xian-cong/Swalk-Stick/JPEG/2 - Content Page.jpg

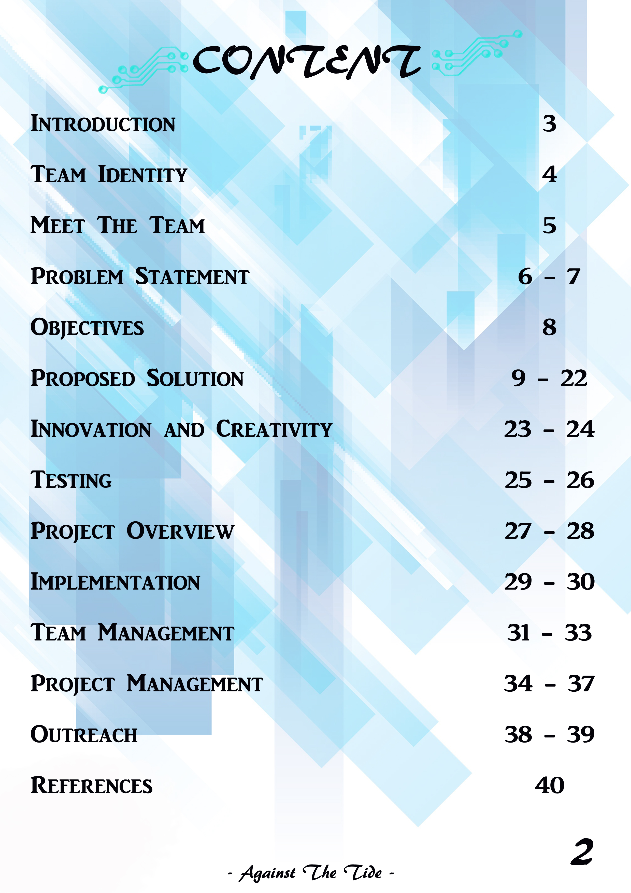
JPEG/2 - Content Page.jpg
