xian-cong/Swalk-Stick/JPEG/4 - Team Identity.jpg

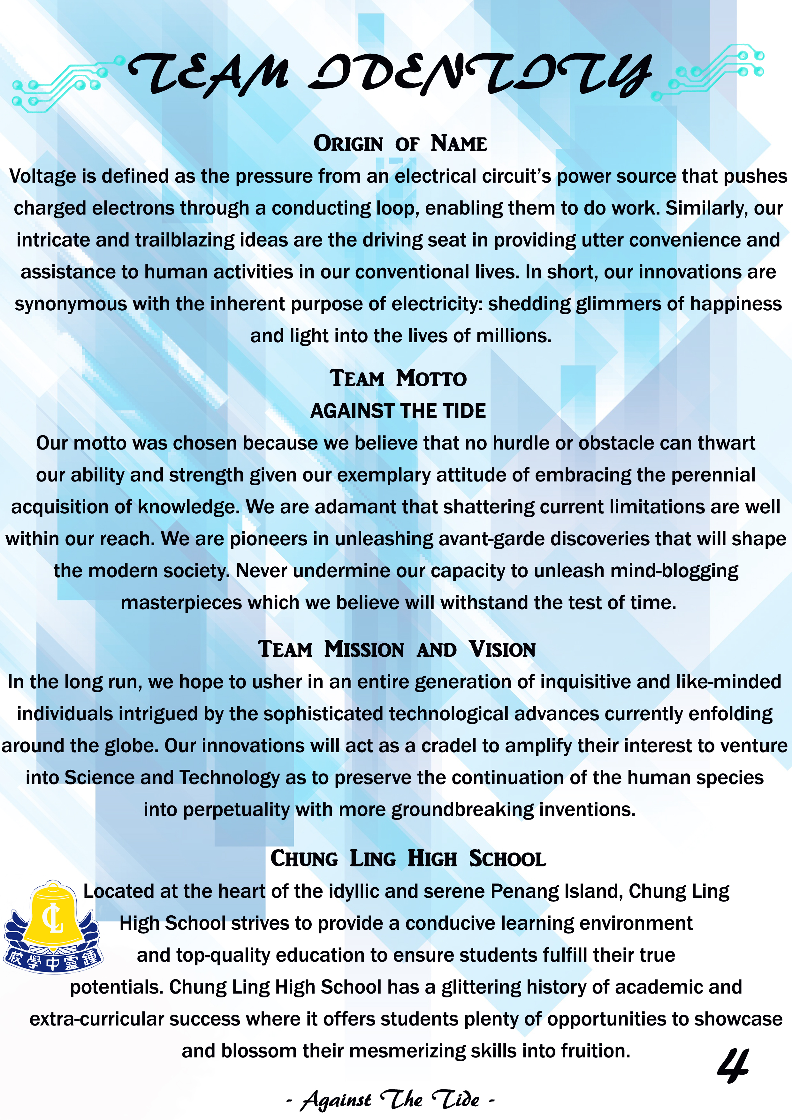
JPEG/4 - Team Identity.jpg
