xian-cong/Swalk-Stick/JPEG/5 - Meet The Team.jpg

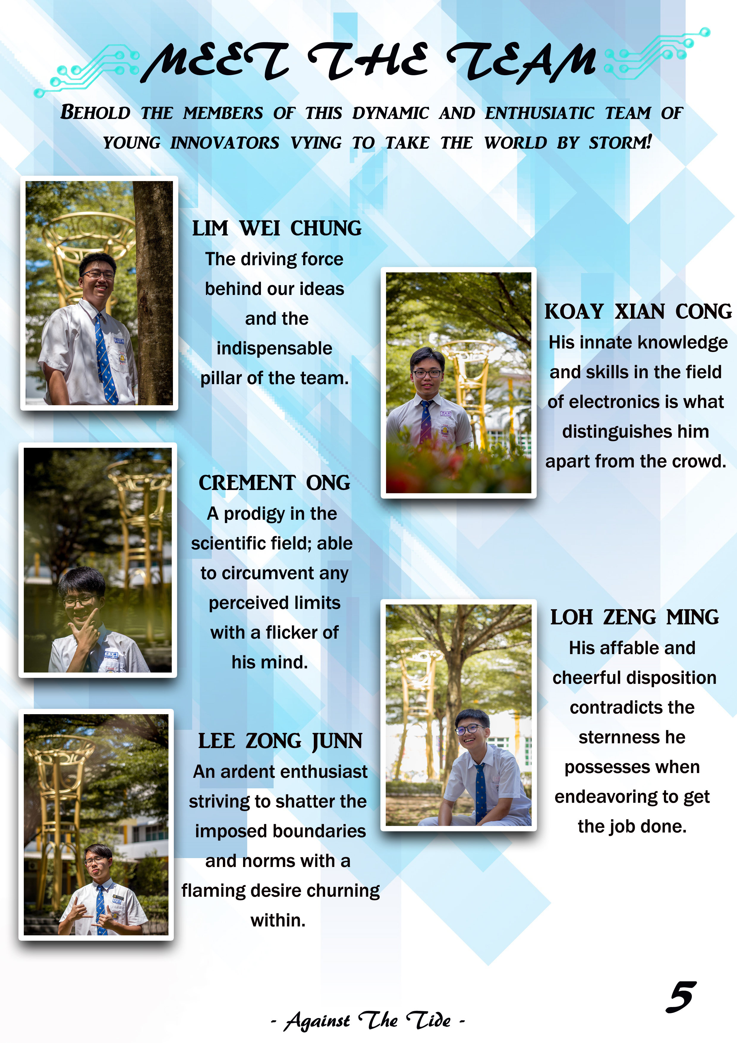
JPEG/5 - Meet The Team.jpg
