xian-cong/Swalk-Stick/JPEG/7 - Problem Statement.jpg

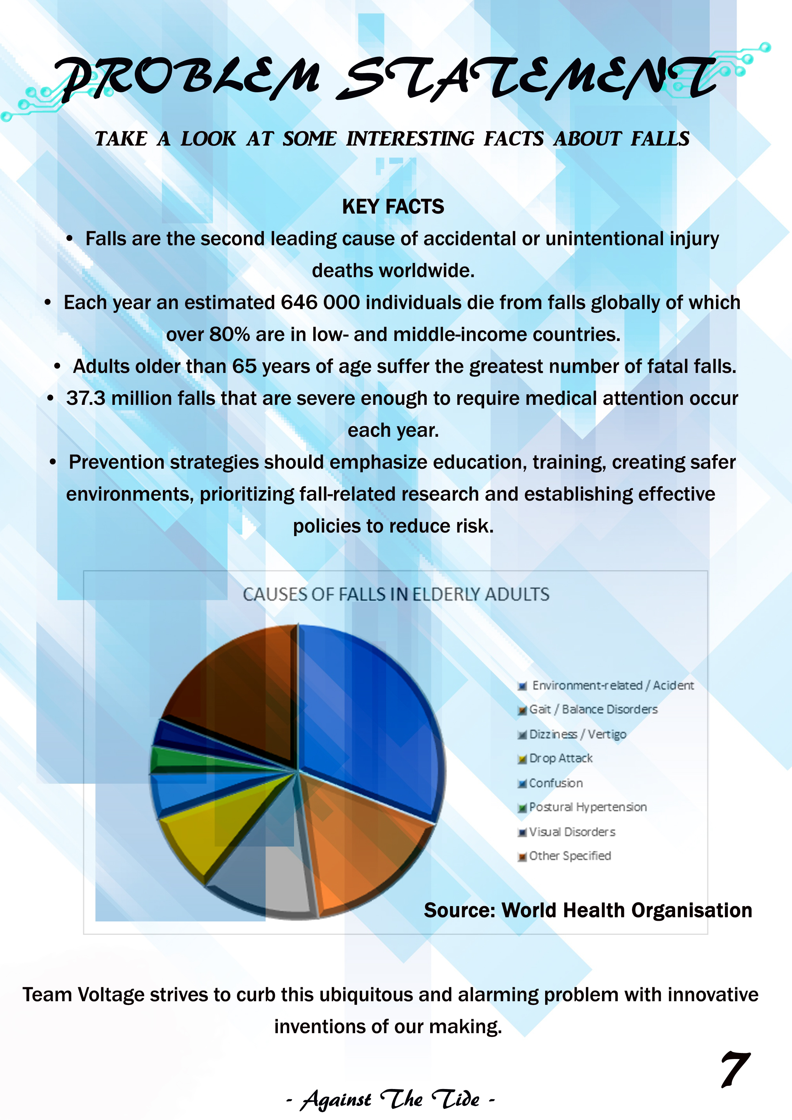
JPEG/7 - Problem Statement.jpg
