xian-cong/Swalk-Stick/JPEG/8 - Objectives.jpg

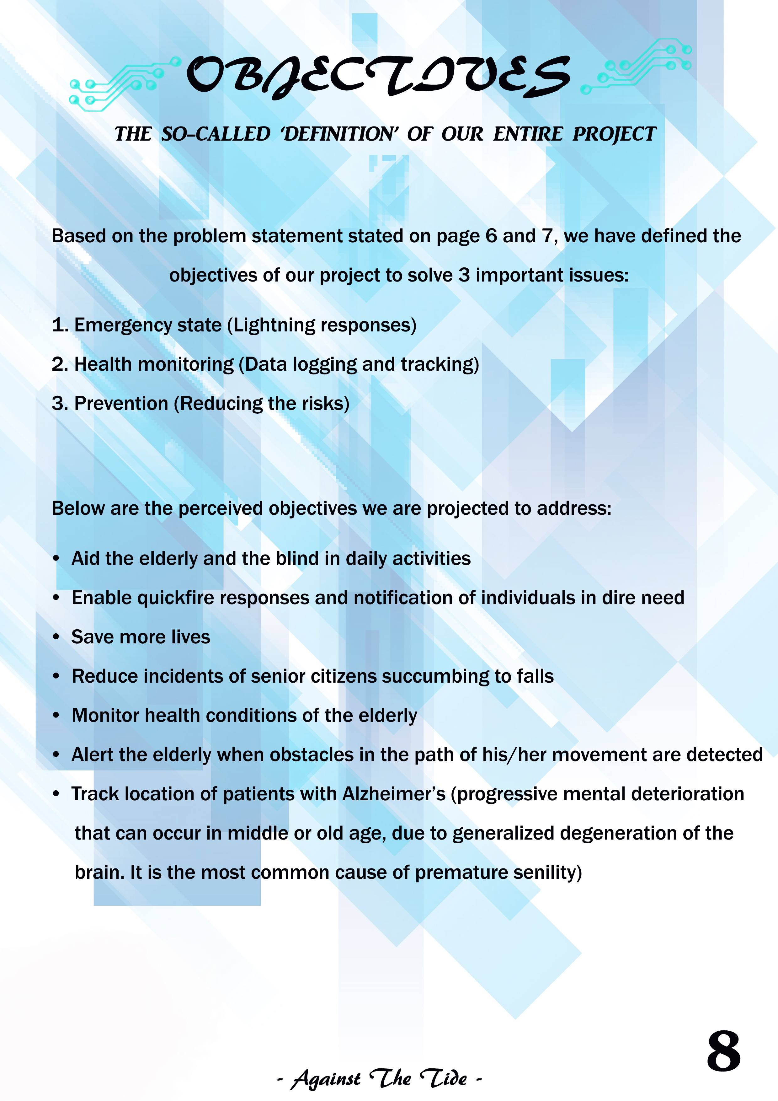
JPEG/8 - Objectives.jpg
