xian-cong/Swalk-Stick/JPEG/11 - Solution (Function).jpg

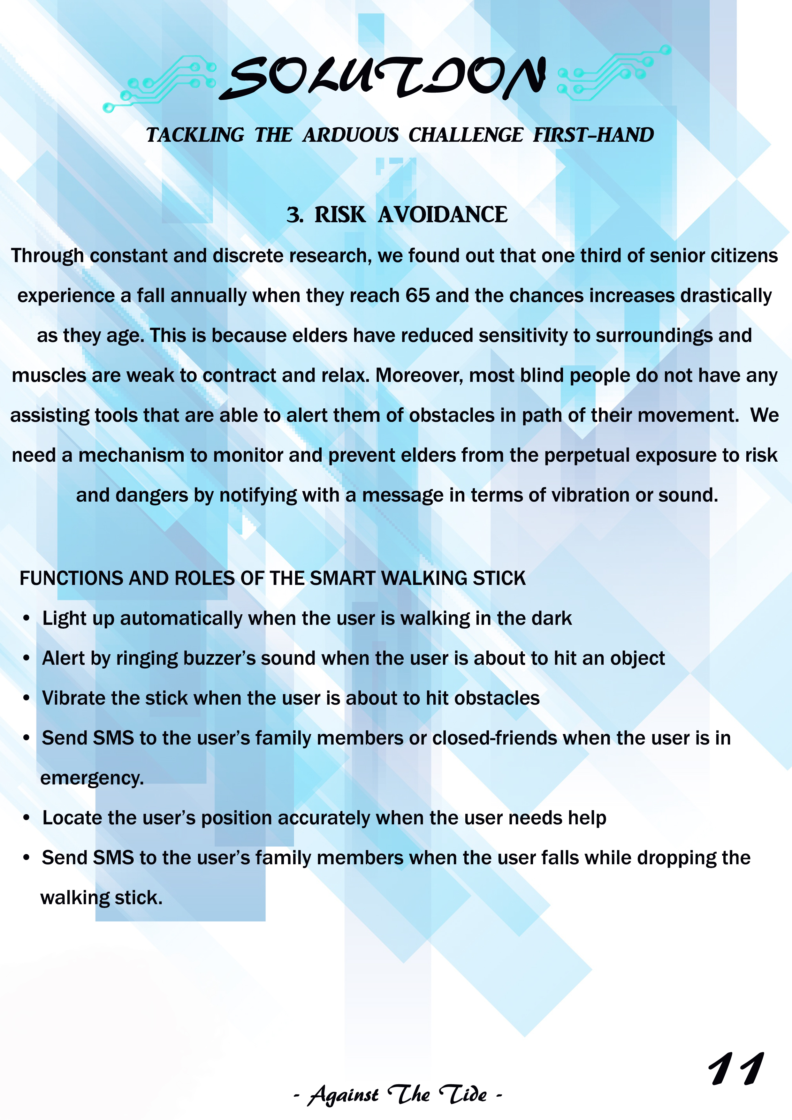
JPEG/11 - Solution (Function).jpg
