xian-cong/Swalk-Stick/JPEG/12 - Solution (Design Specifications).jpg

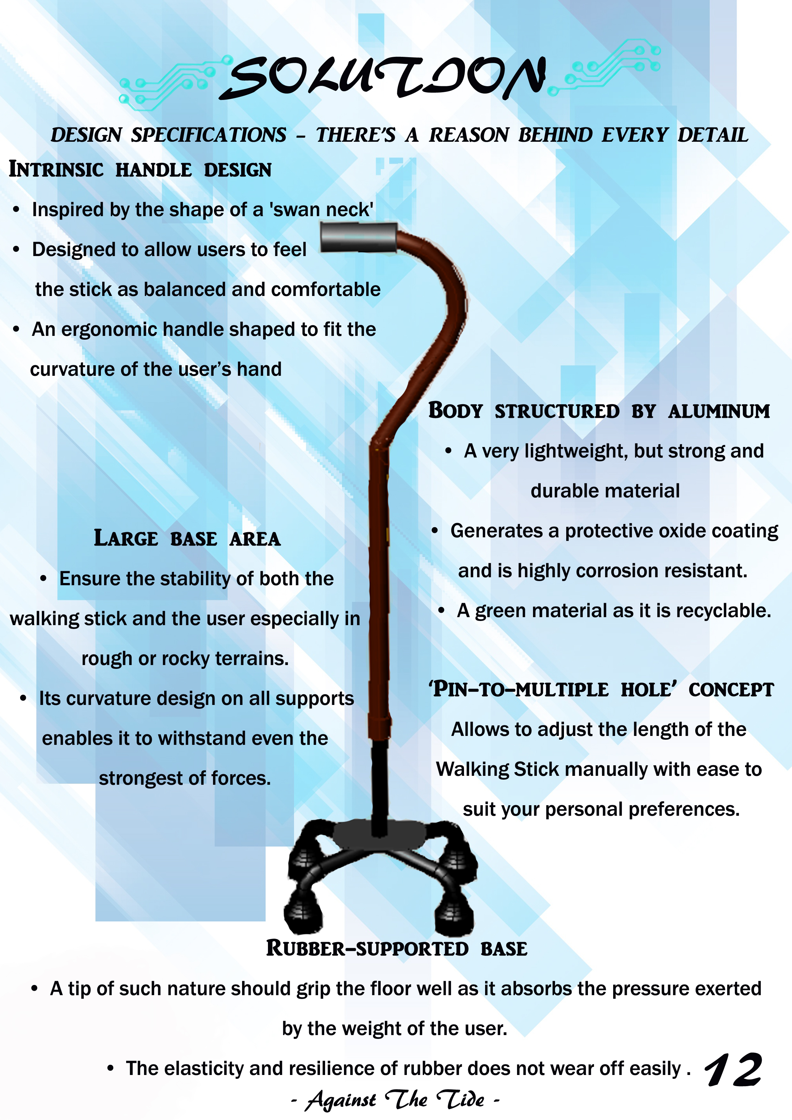
JPEG/12 - Solution (Design Specifications).jpg
