xian-cong/Swalk-Stick/JPEG/14 - Solution (Hardware I).jpg

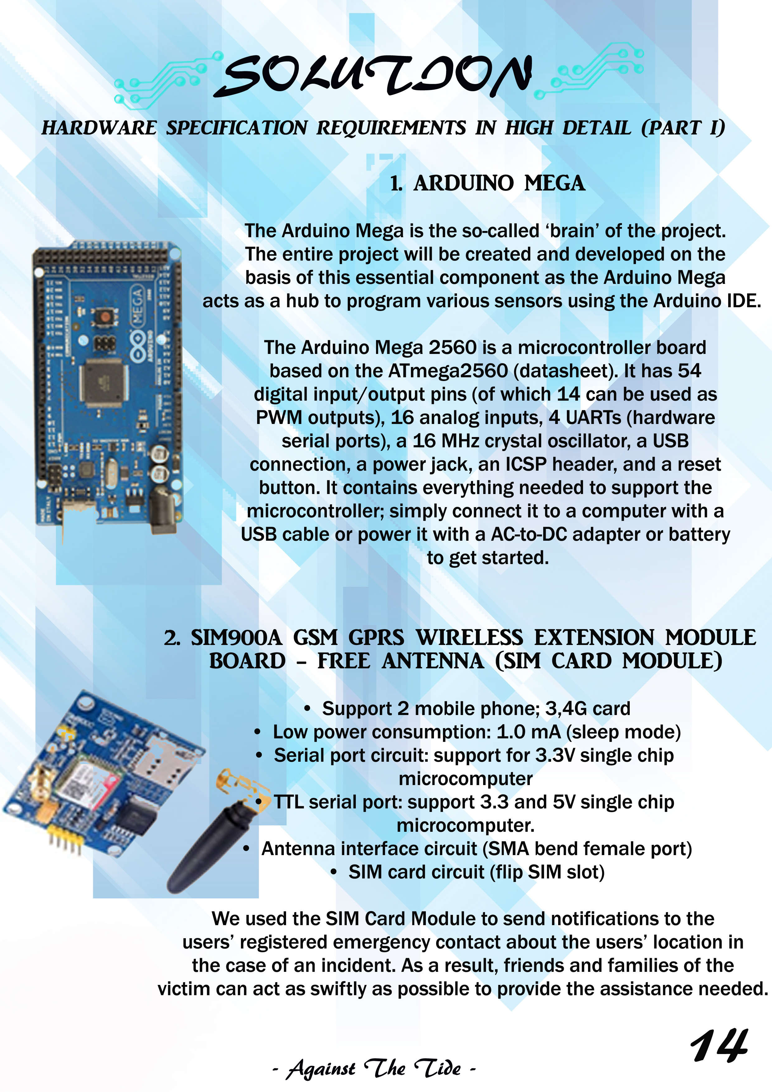
JPEG/14 - Solution (Hardware I).jpg
