xian-cong/Swalk-Stick/JPEG/16 - Solution (Hardware III).jpg

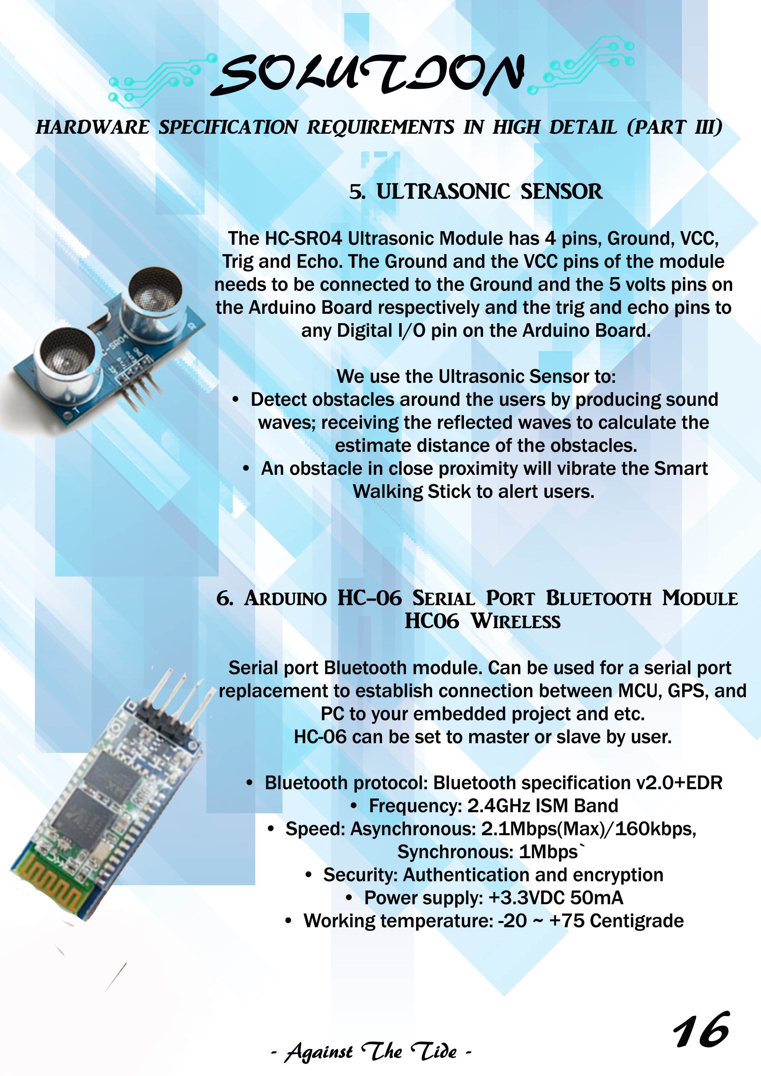
JPEG/16 - Solution (Hardware III).jpg
