xian-cong/Swalk-Stick/JPEG/17 - Solution (Hardware IV).jpg

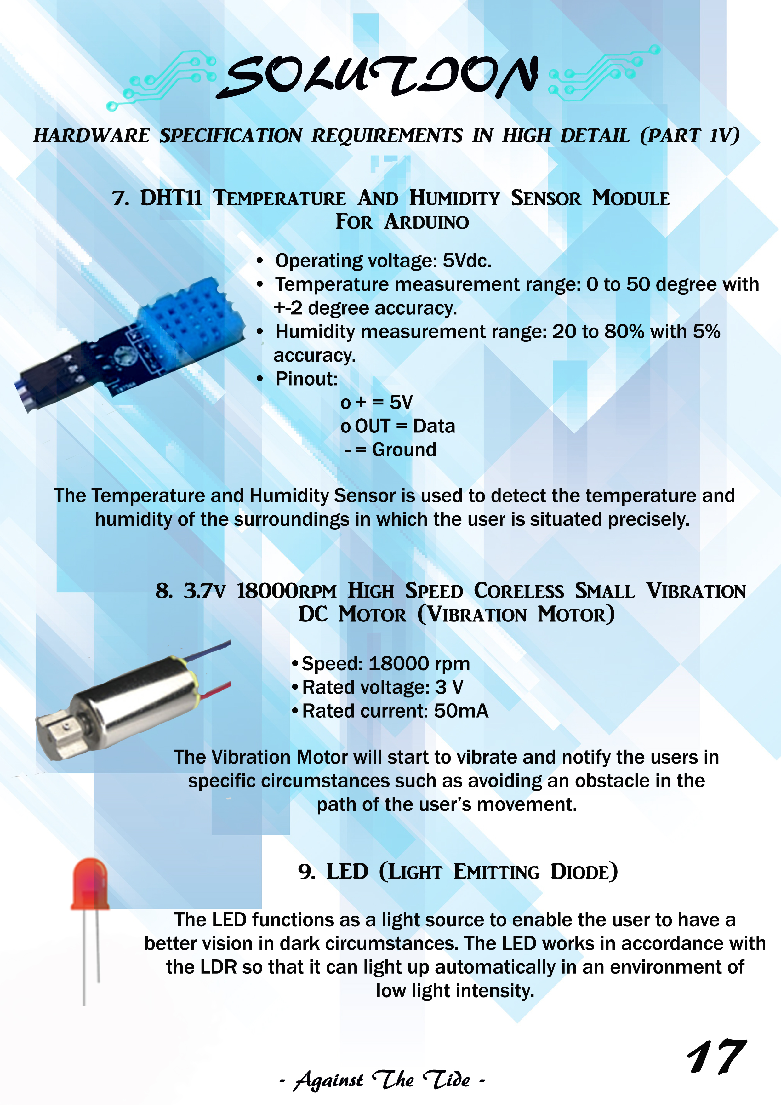
JPEG/17 - Solution (Hardware IV).jpg
