xian-cong/Swalk-Stick/JPEG/22 -Solution (Summary).jpg

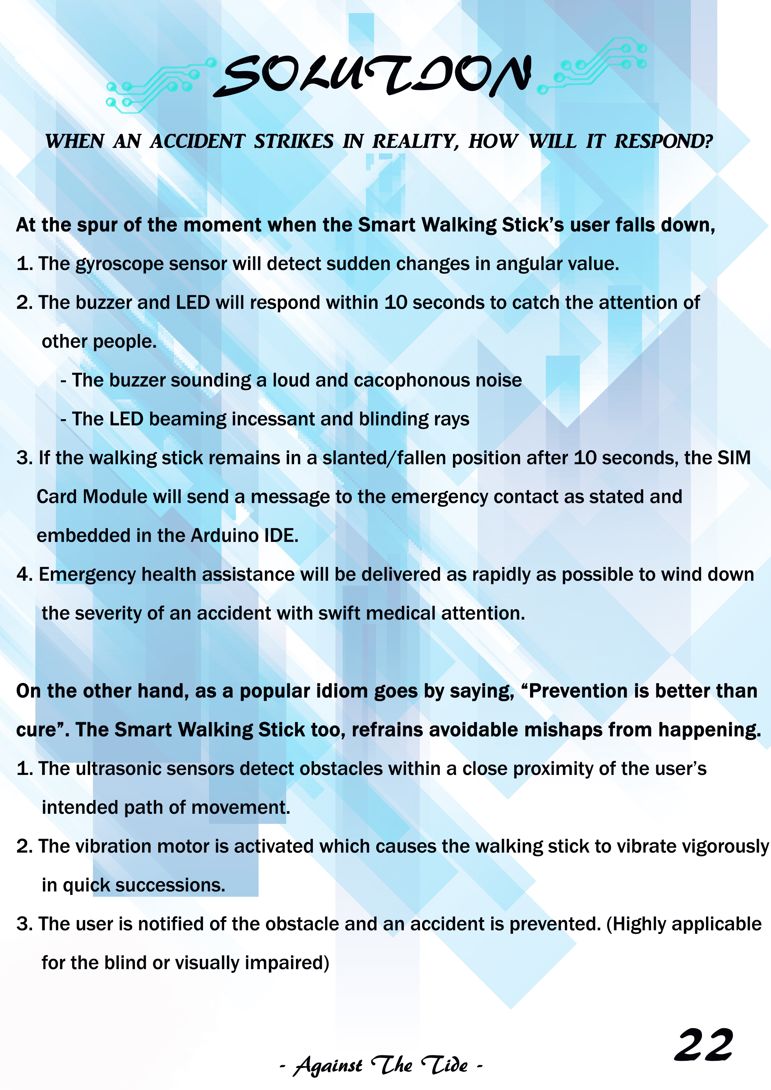
JPEG/22 -Solution (Summary).jpg
