xian-cong/Swalk-Stick/JPEG/23 - Creativity and Innovation.jpg

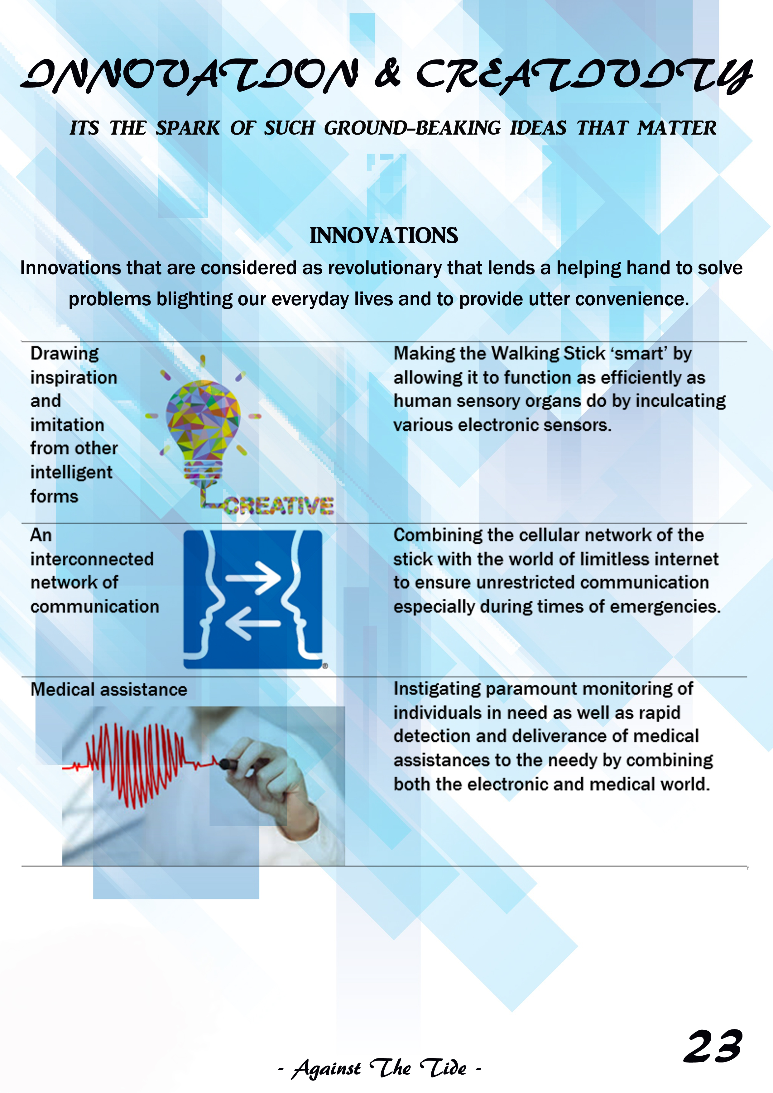
JPEG/23 - Creativity and Innovation.jpg
