xian-cong/Swalk-Stick/JPEG/24 - Innovation and Creativity II.jpg

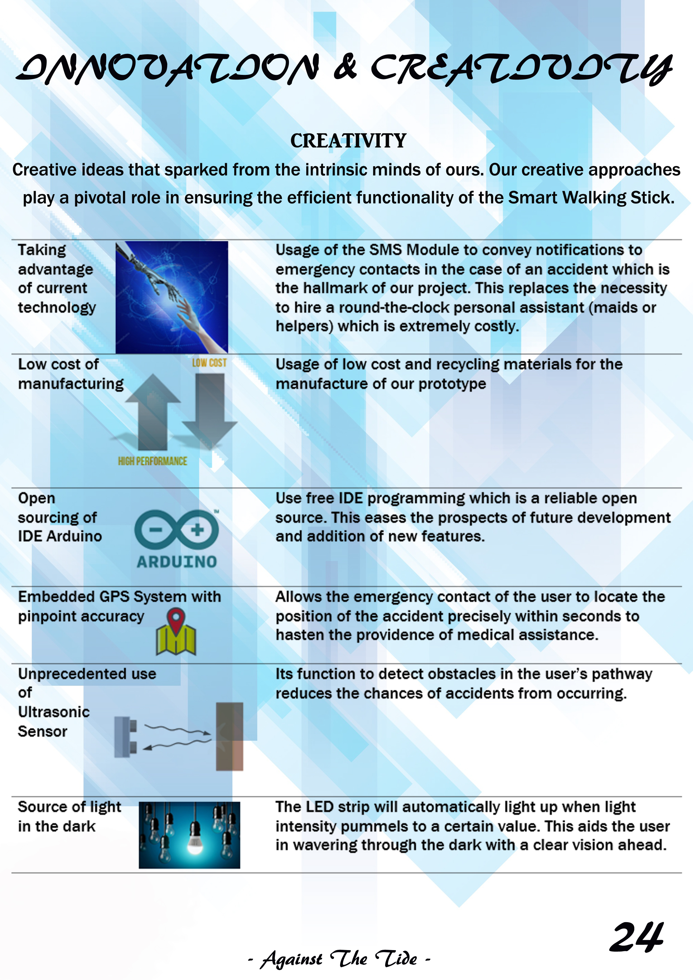
JPEG/24 - Innovation and Creativity II.jpg
