xian-cong/Swalk-Stick/JPEG/27 - Project Overview I.jpg

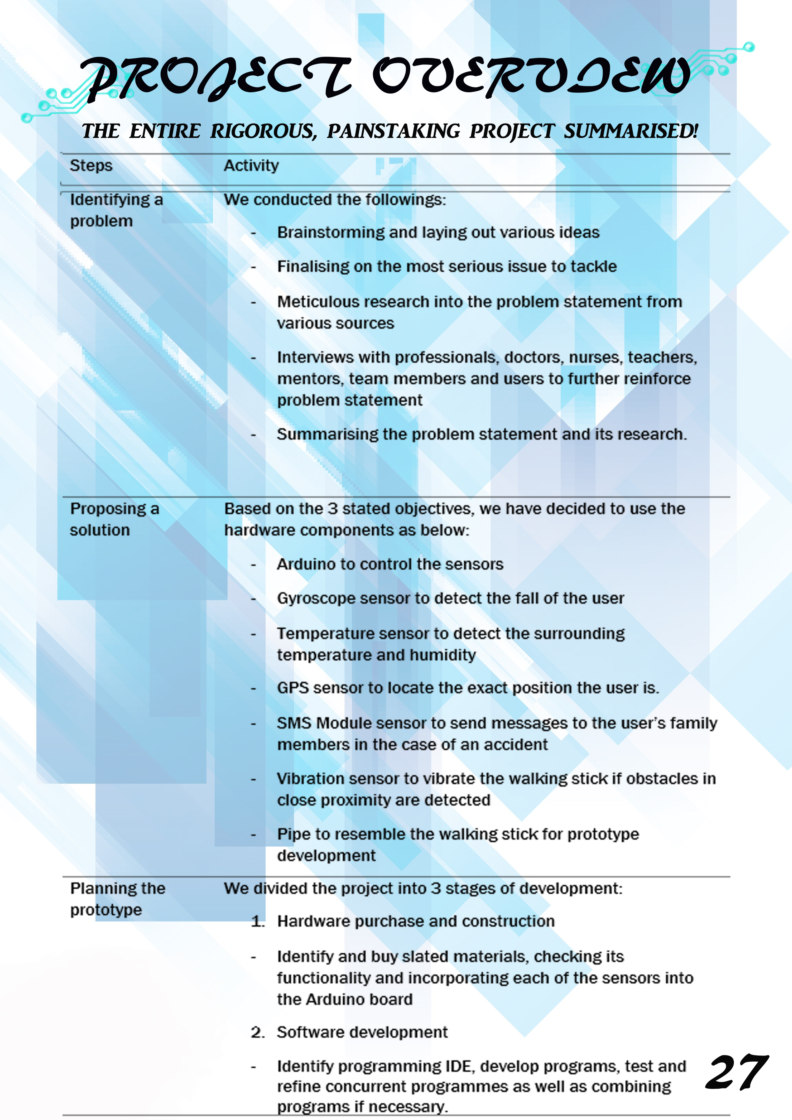
JPEG/27 - Project Overview I.jpg
