xian-cong/Swalk-Stick/JPEG/29 - Implementation I.jpg

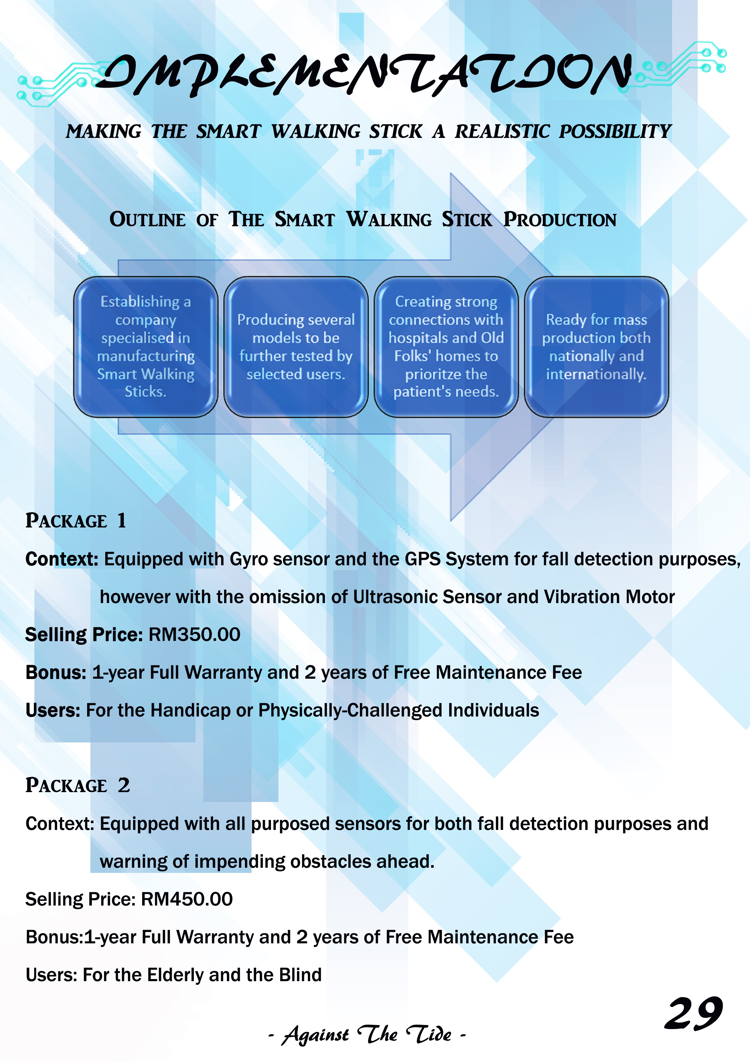
JPEG/29 - Implementation I.jpg
