xian-cong/Swalk-Stick/JPEG/30 - Implementation II.jpg

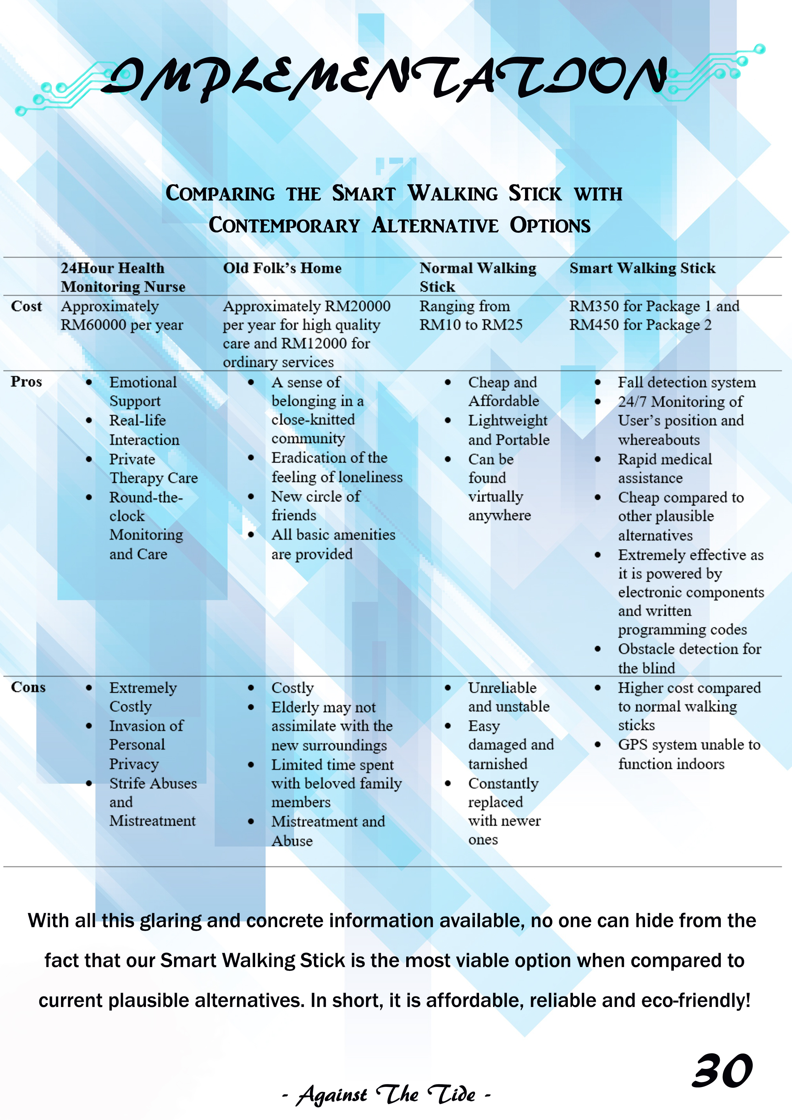
JPEG/30 - Implementation II.jpg
