xian-cong/Swalk-Stick/JPEG/31 - Team Management I.jpg

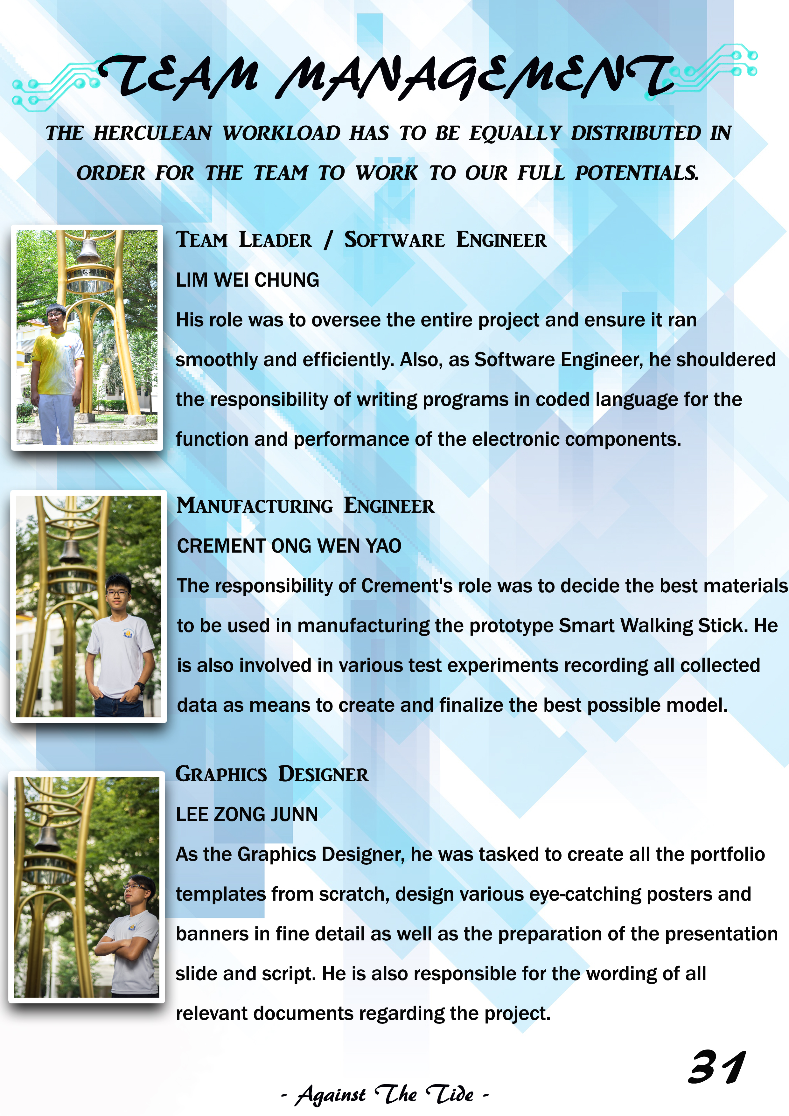
JPEG/31 - Team Management I.jpg
