xian-cong/Swalk-Stick/JPEG/32 - Team Management II.jpg

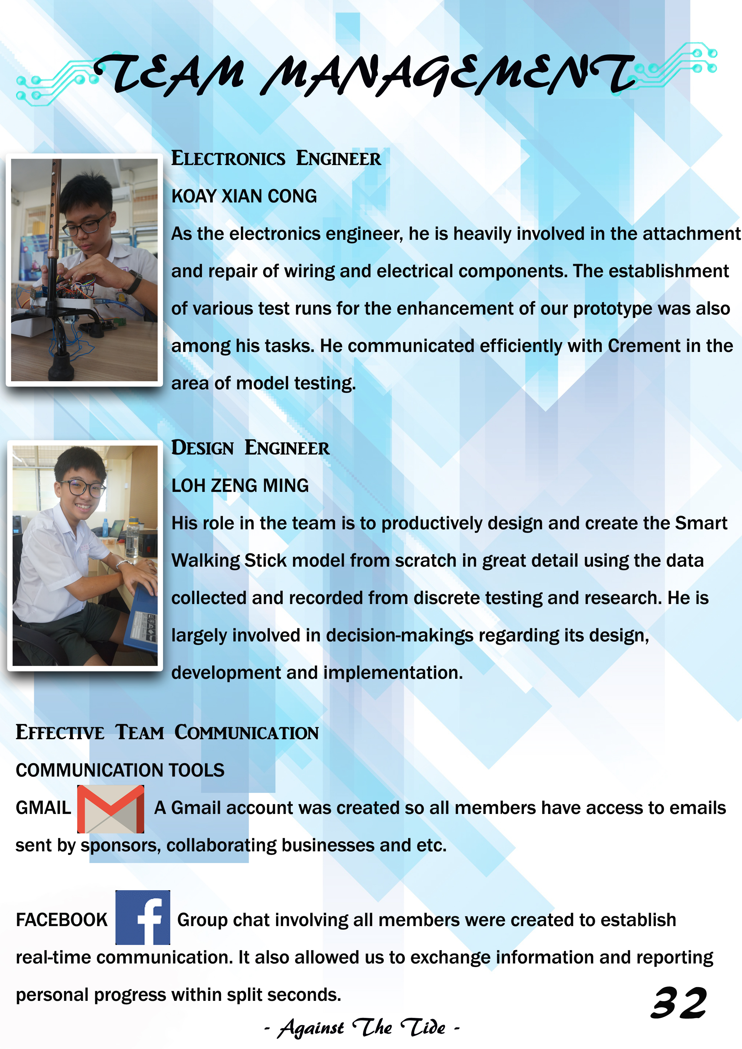
JPEG/32 - Team Management II.jpg
