xian-cong/Swalk-Stick/JPEG/33 - Team Management III.jpg

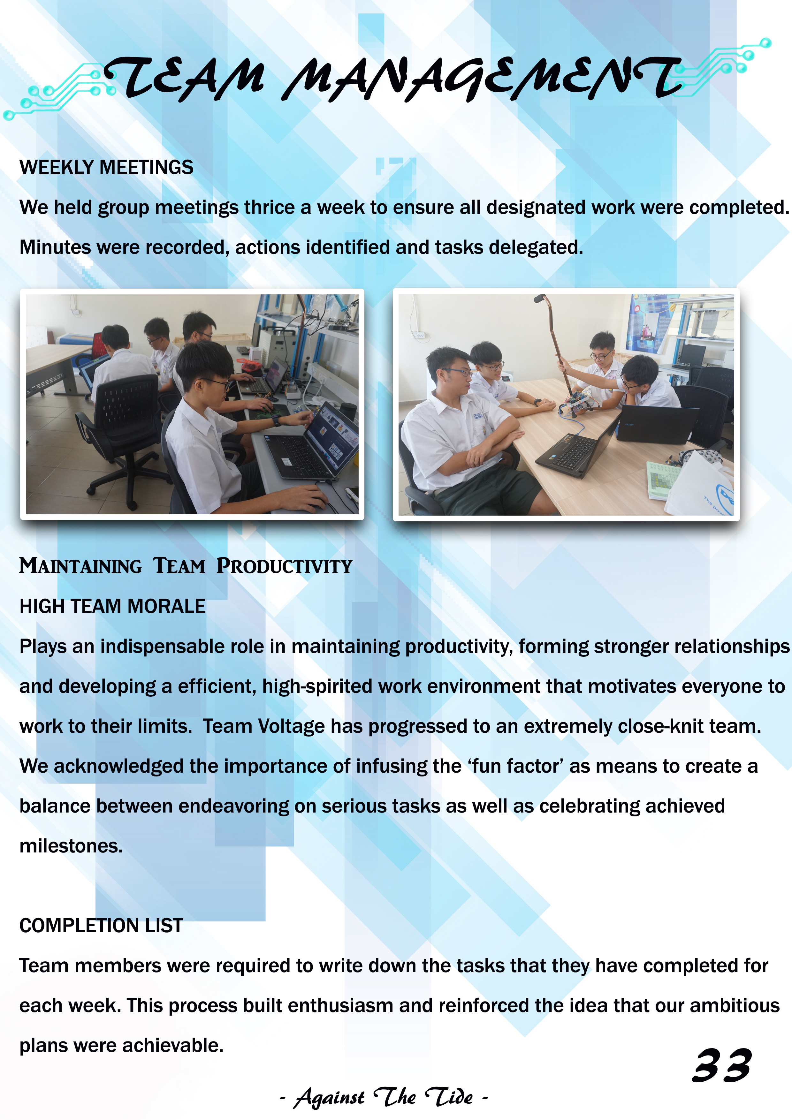
JPEG/33 - Team Management III.jpg
