xian-cong/Swalk-Stick/JPEG/34 - Project Management I.jpg

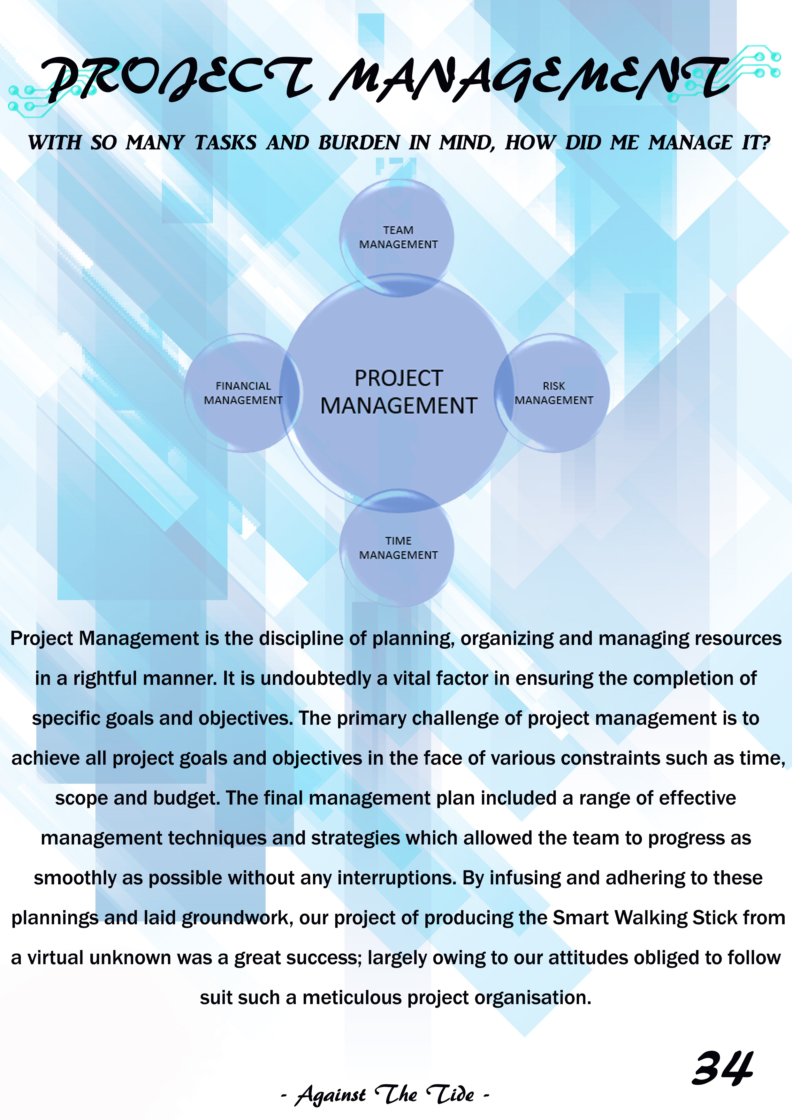
JPEG/34 - Project Management I.jpg
