xian-cong/Swalk-Stick/JPEG/35 - Project Management II.jpg

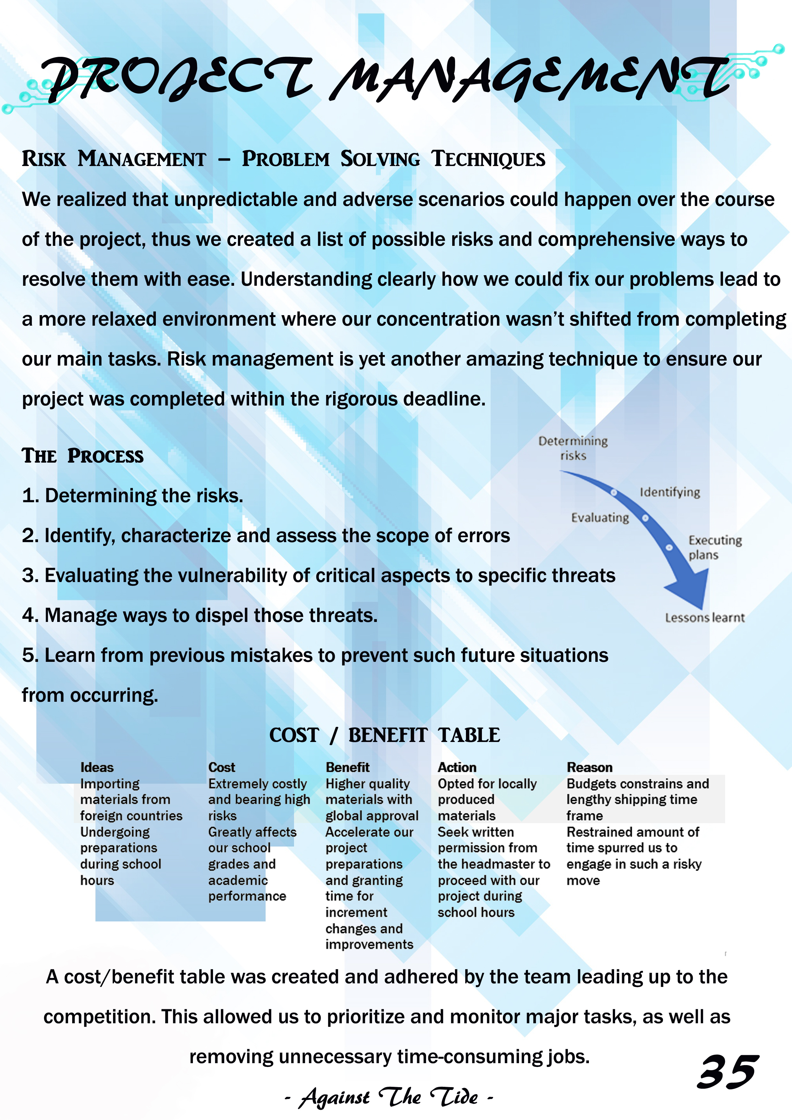
JPEG/35 - Project Management II.jpg
