xian-cong/Swalk-Stick/JPEG/36 - Project Management III.jpg

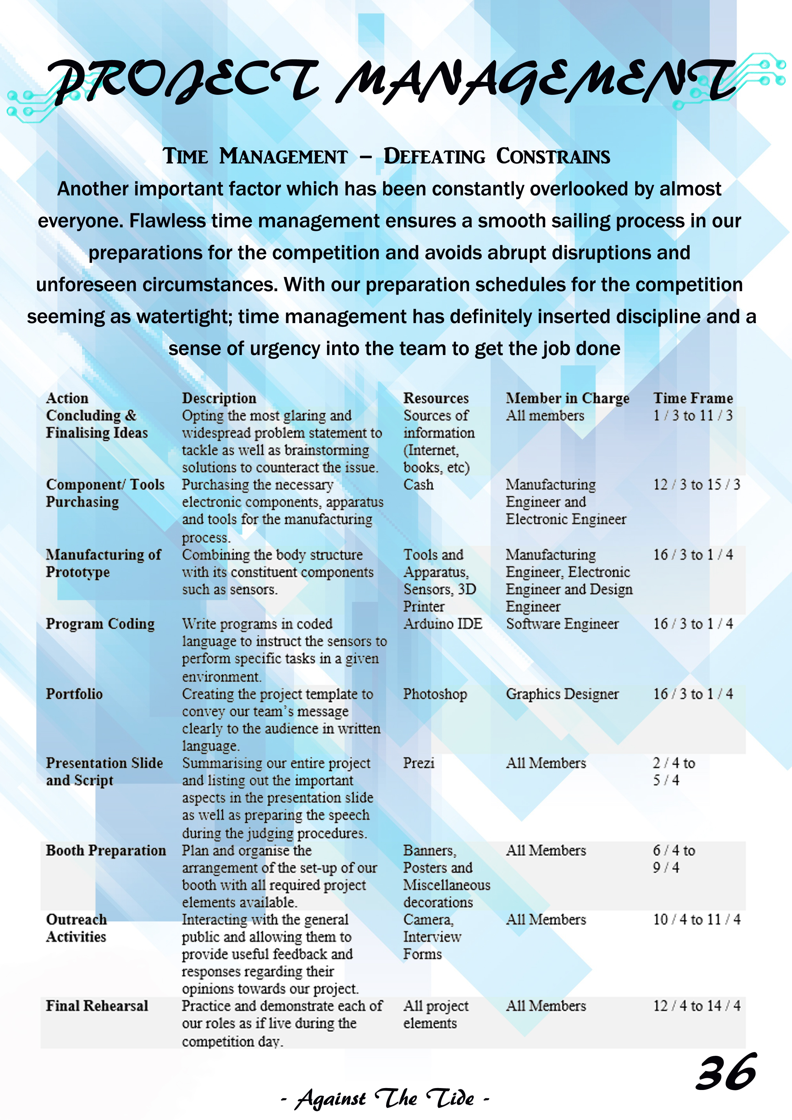
JPEG/36 - Project Management III.jpg
