xian-cong/Swalk-Stick/JPEG/37 - Project Management IV.jpg

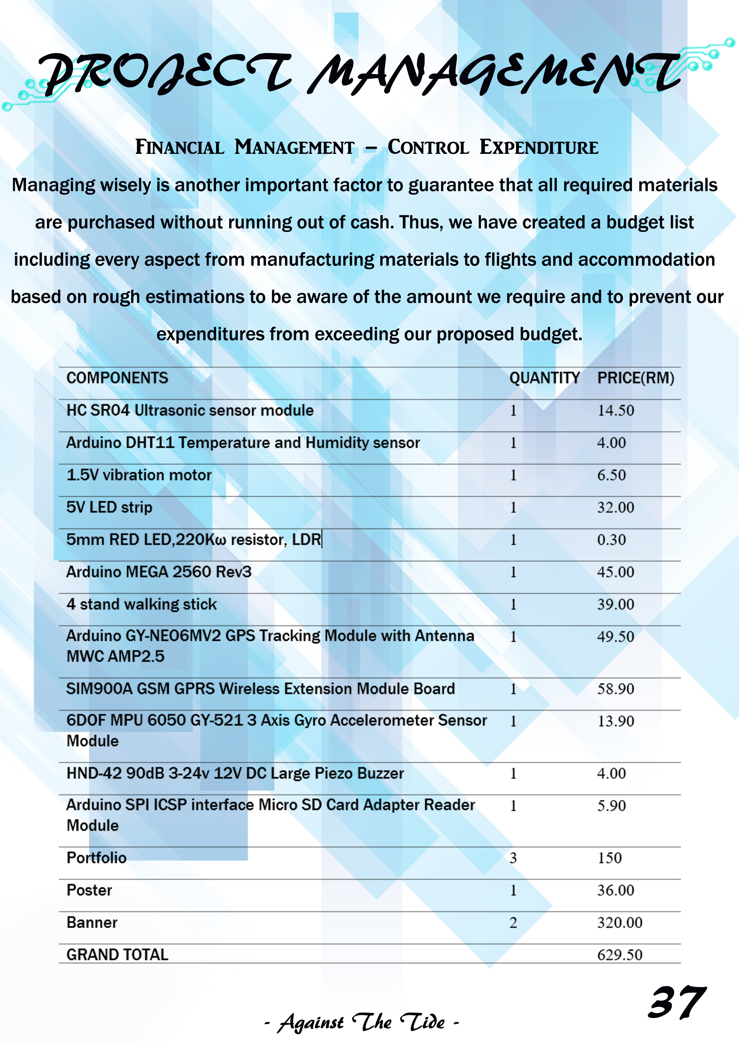
JPEG/37 - Project Management IV.jpg
