xian-cong/Swalk-Stick/JPEG/38 - Outreach.jpg

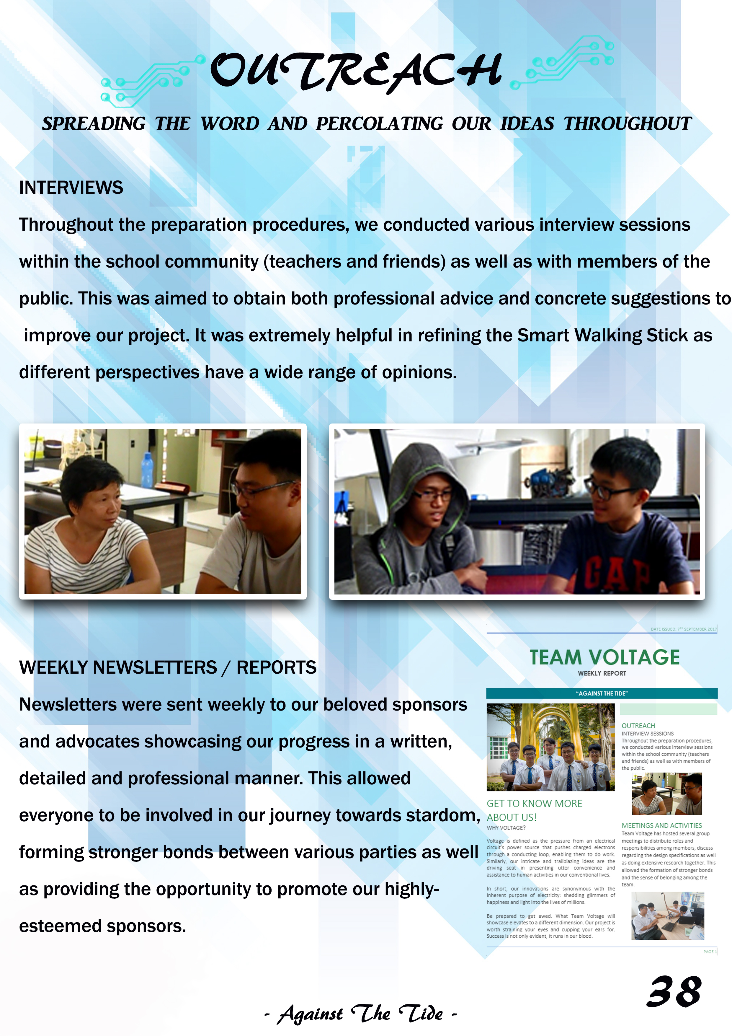
JPEG/38 - Outreach.jpg
