xian-cong/Swalk-Stick/JPEG/39 - Outreach II.jpg

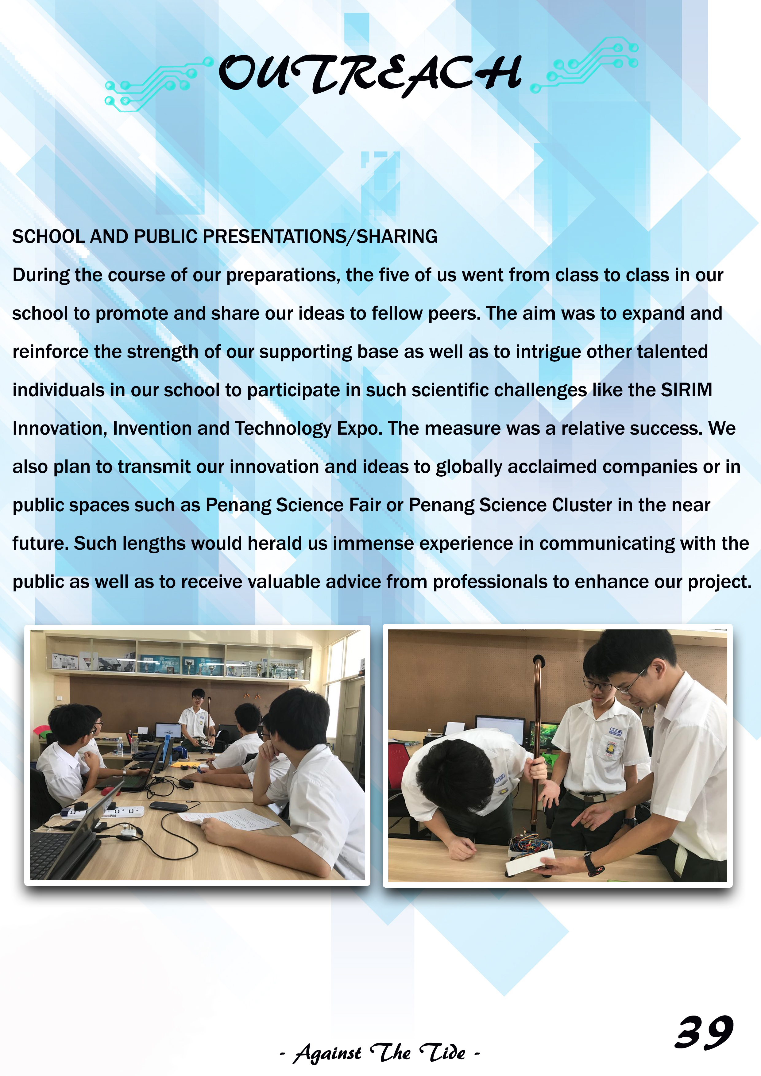
JPEG/39 - Outreach II.jpg
