xian-cong/Swalk-Stick/JPEG/40 - References.jpg

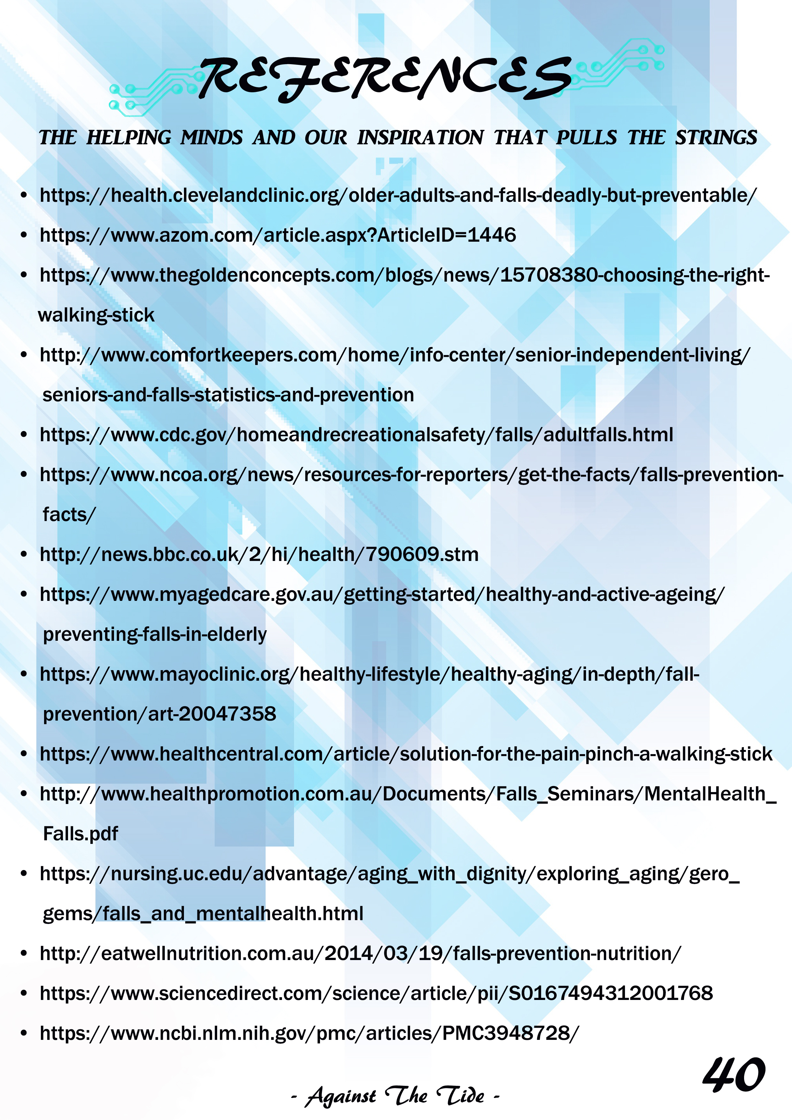
JPEG/40 - References.jpg
