xian-cong/Swalk-Stick/Photos/29634891_10212143320402441_1095436665_o.jpg

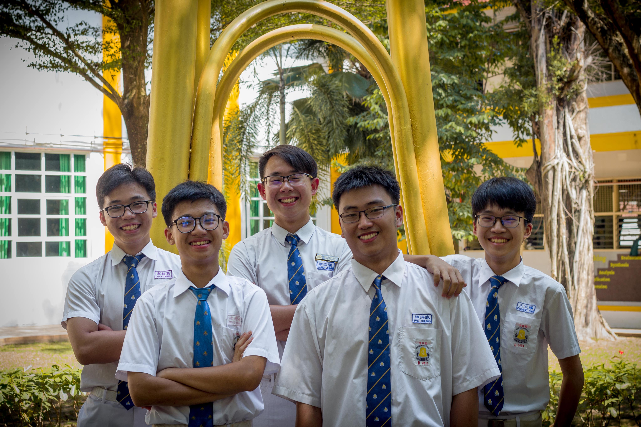
Photos/29634891_10212143320402441_1095436665_o.jpg
