xian-cong/Swalk-Stick/Photos/29680679_10212143319682423_1693739212_o.jpg

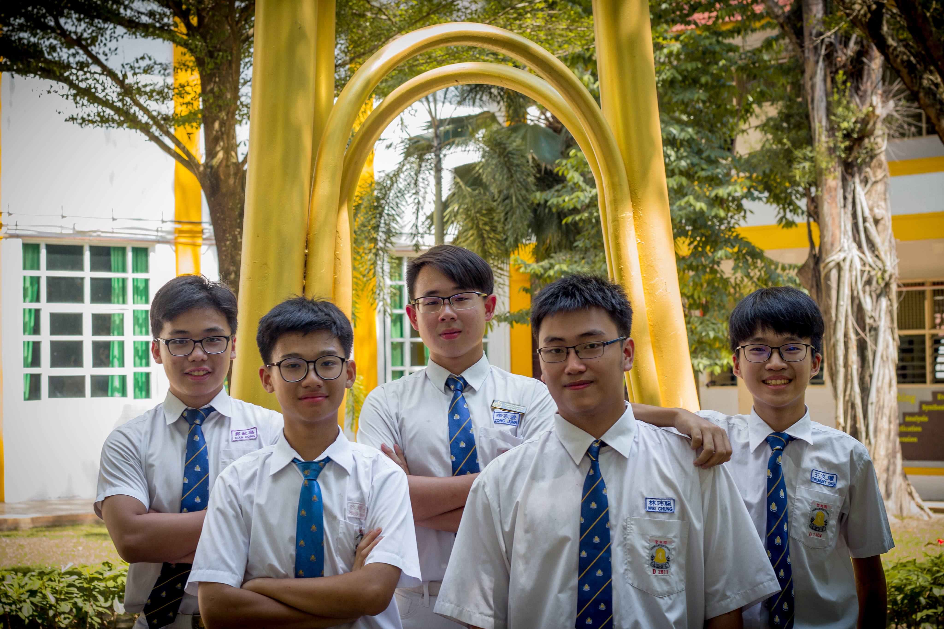
Photos/29680679_10212143319682423_1693739212_o.jpg
