xian-cong/Swalk-Stick/Photos/29681004_10212143318042382_196674917_o.jpg

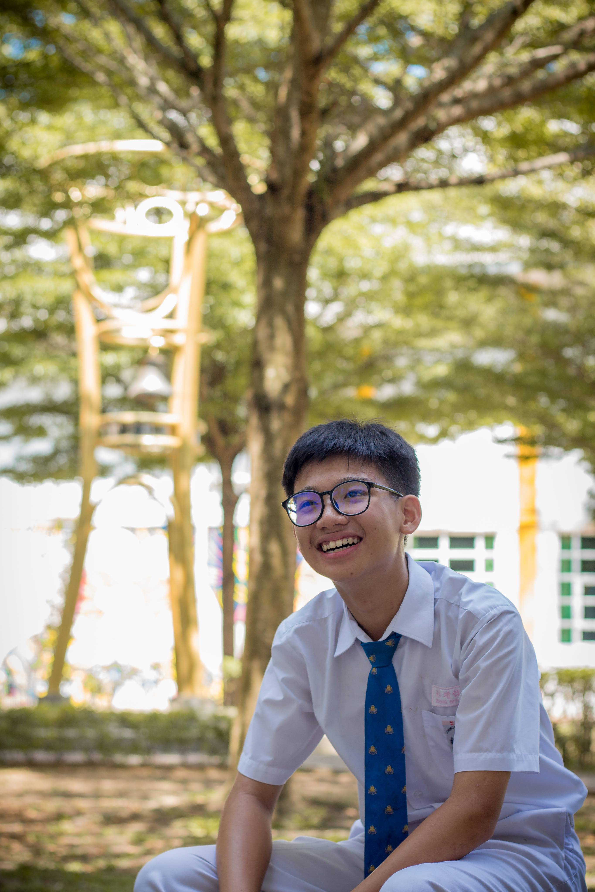
Photos/29681004_10212143318042382_196674917_o.jpg
