xian-cong/Swalk-Stick/Photos/29747121_1145777738895164_963517210_o.jpg

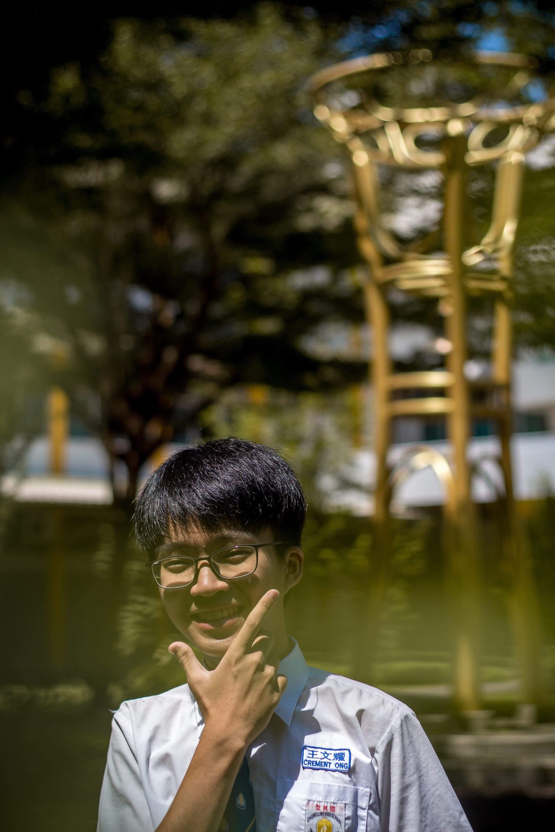
Photos/29747121_1145777738895164_963517210_o.jpg
