xian-cong/Swalk-Stick/Photos/29747382_10212143314962305_1216166150_o.jpg

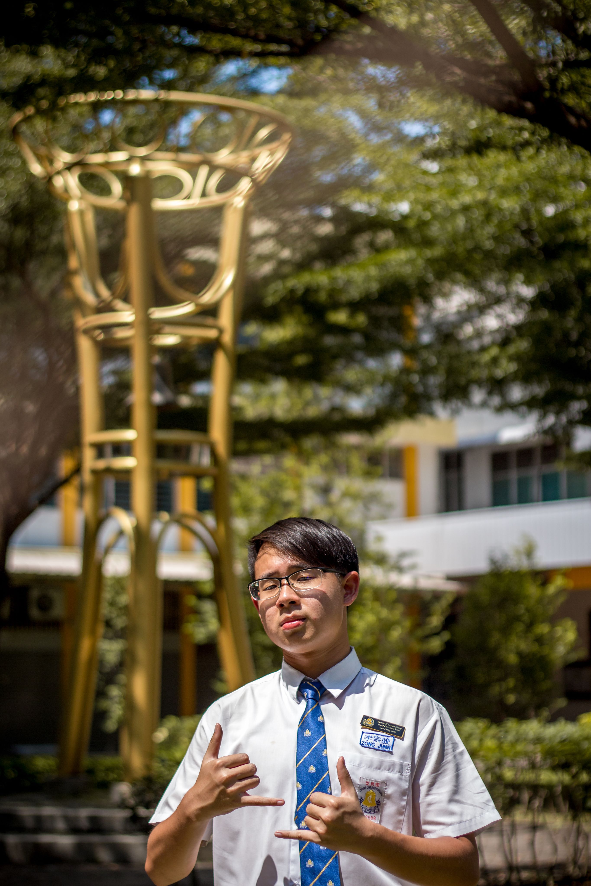
Photos/29747382_10212143314962305_1216166150_o.jpg
