xian-cong/Swalk-Stick/Photos/29748040_10212143311642222_1830464331_o.jpg

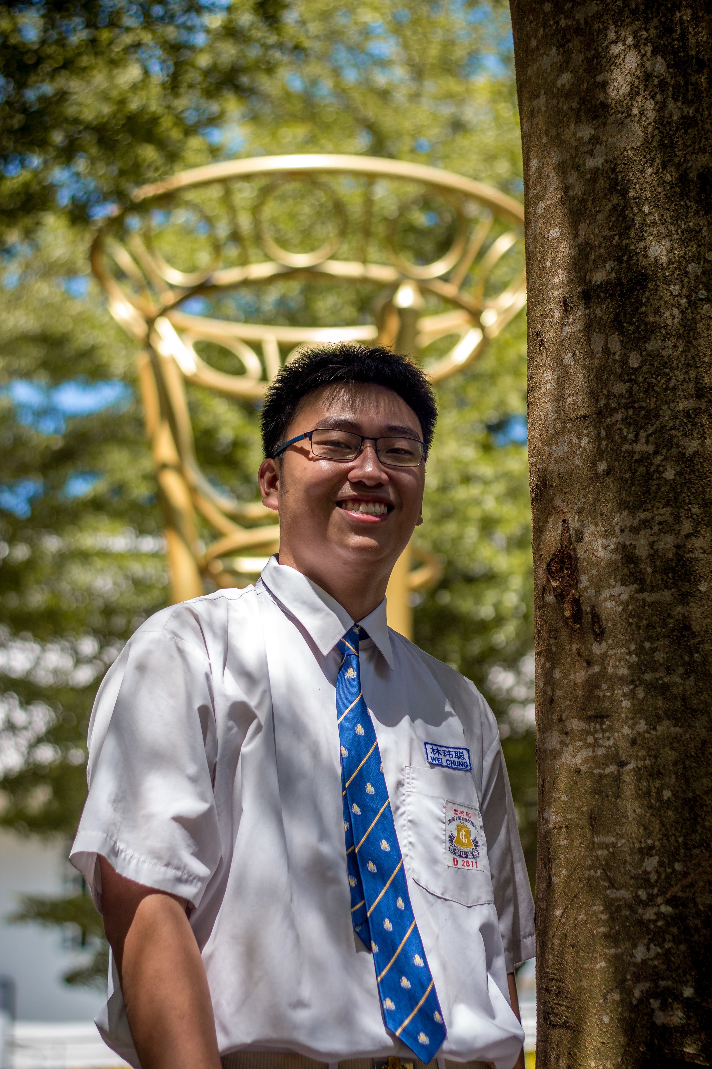
Photos/29748040_10212143311642222_1830464331_o.jpg
