xian-cong/Swalk-Stick/Photos/29748860_10212143317402366_1311559309_o.jpg

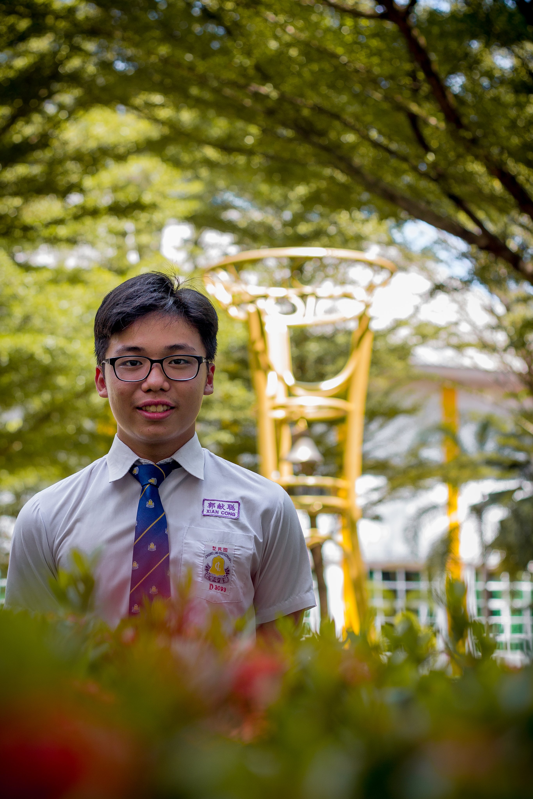
Photos/29748860_10212143317402366_1311559309_o.jpg
