xian-cong/Swalk-Stick/Photos/DSC05823.JPG

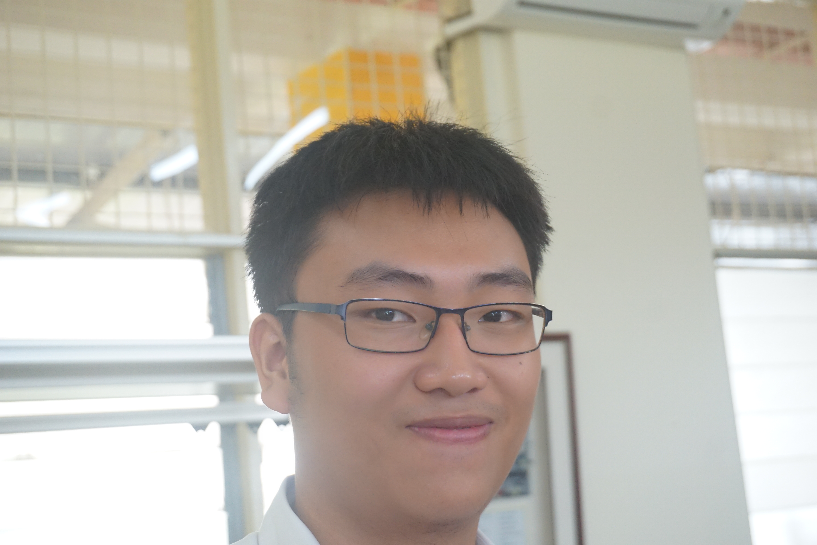
Photos/DSC05823.JPG
