xian-cong/Swalk-Stick/Photos/IMG_20170608_174837.jpg

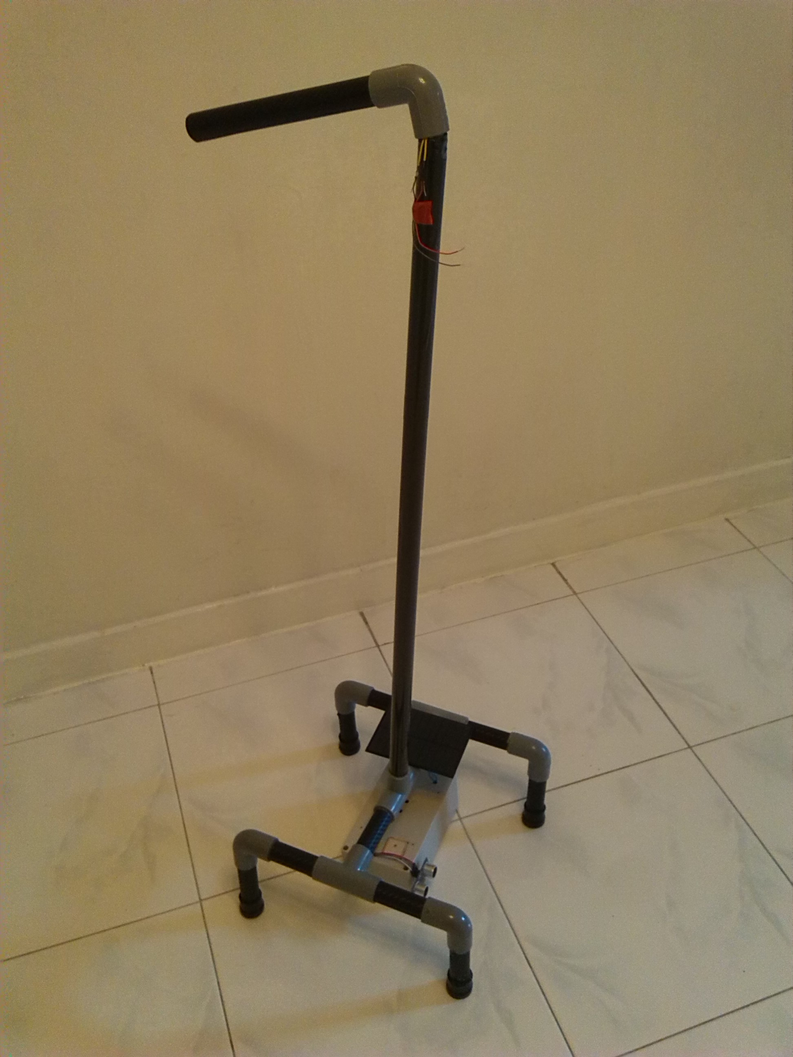
Photos/IMG_20170608_174837.jpg
