xian-cong/Swalk-Stick/JPEG/19 - Solution (Operation and Maintenance Guide).jpg

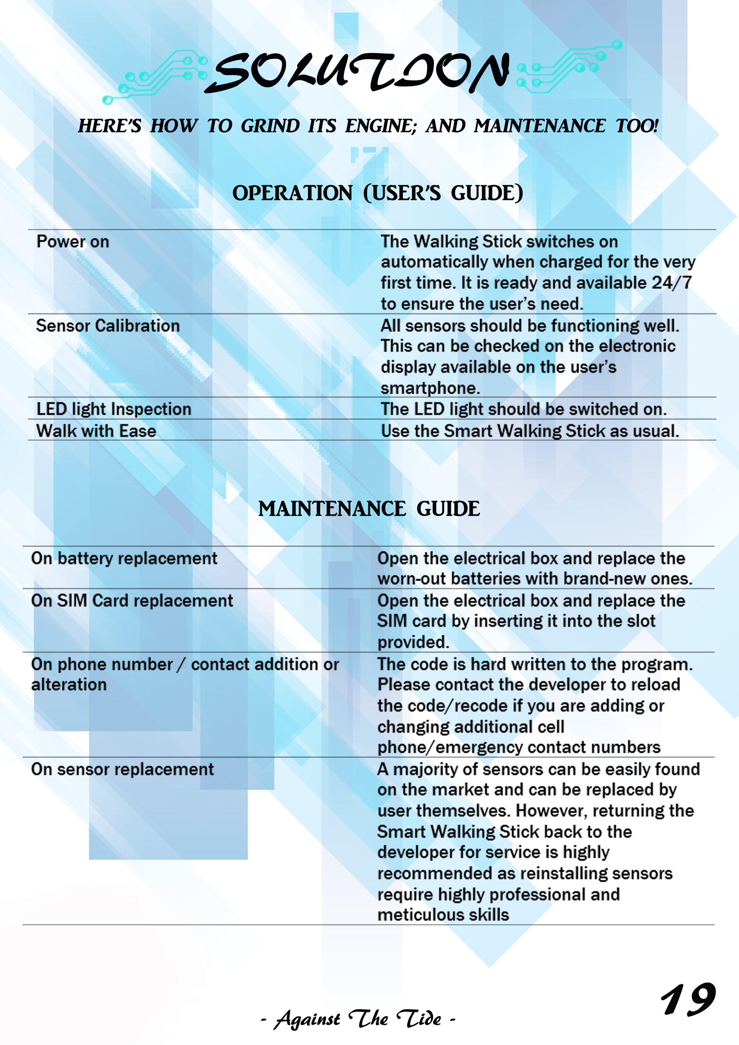
JPEG/19 - Solution (Operation and Maintenance Guide).jpg
