xian-cong/Swalk-Stick/JPEG/20 - Solution (Manufacturing).jpg

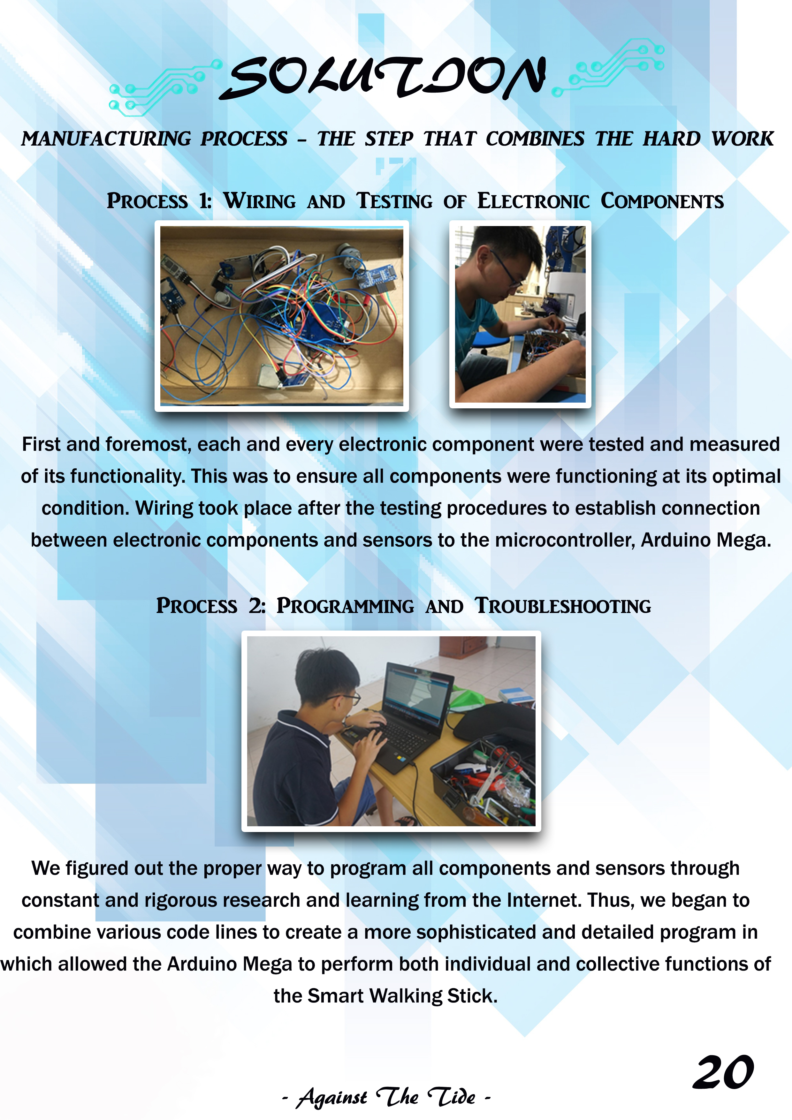
JPEG/20 - Solution (Manufacturing).jpg
