xian-cong/Swalk-Stick/JPEG/21 - Solution (Manufacturing II).jpg

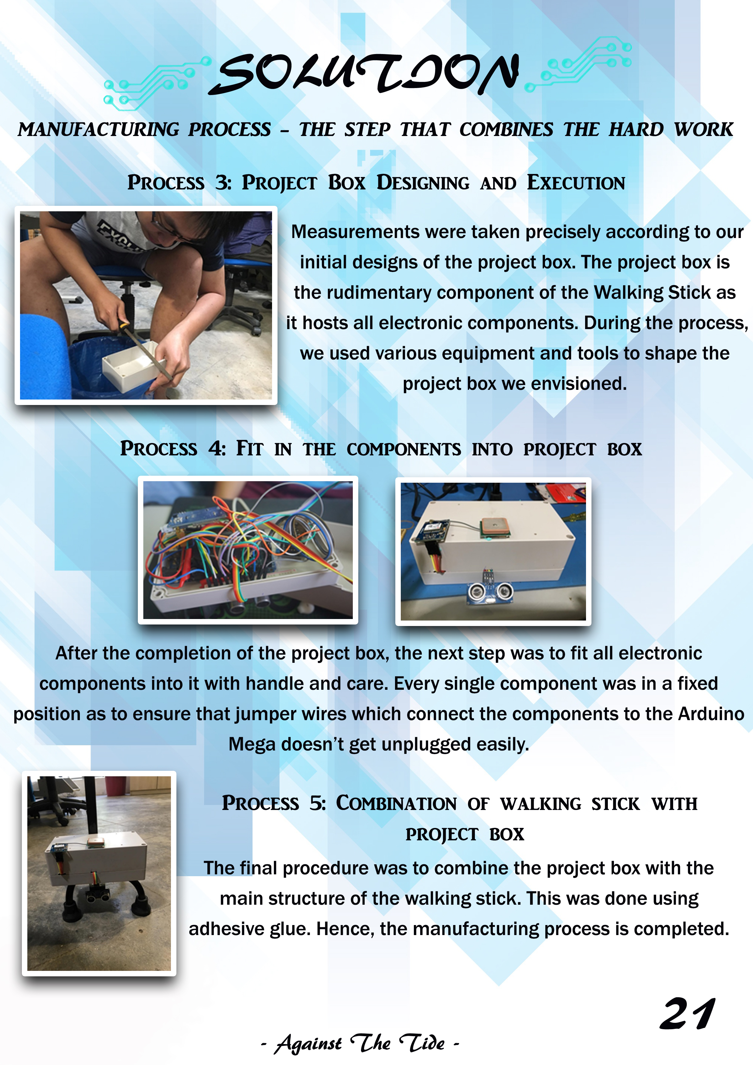
JPEG/21 - Solution (Manufacturing II).jpg
