xian-cong/Swalk-Stick/JPEG/25 - Testing I.jpg

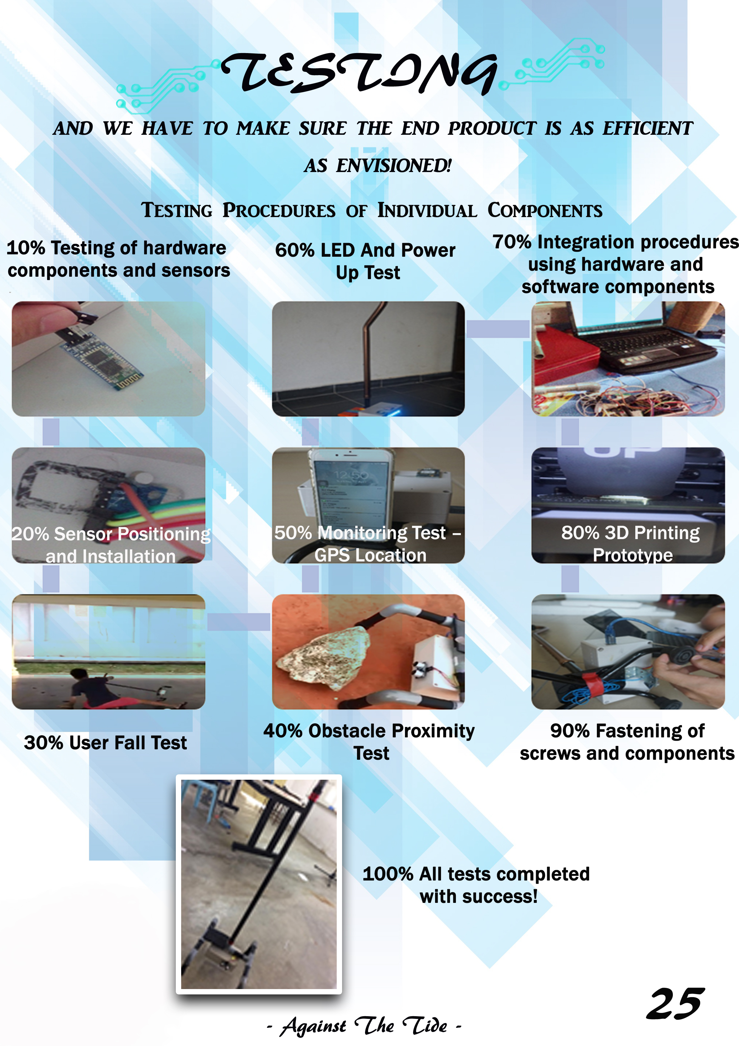
JPEG/25 - Testing I.jpg
