xian-cong/Swalk-Stick/JPEG/26 - Testing II.jpg

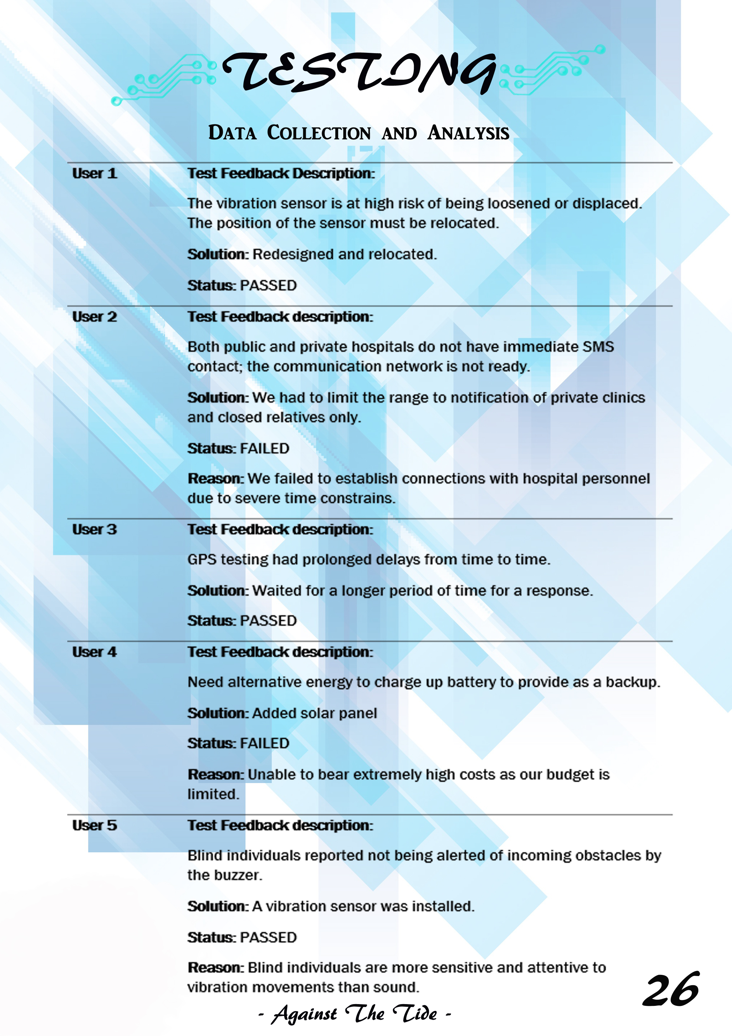
JPEG/26 - Testing II.jpg
