xian-cong/Swalk-Stick/Photos/DSC05798.JPG

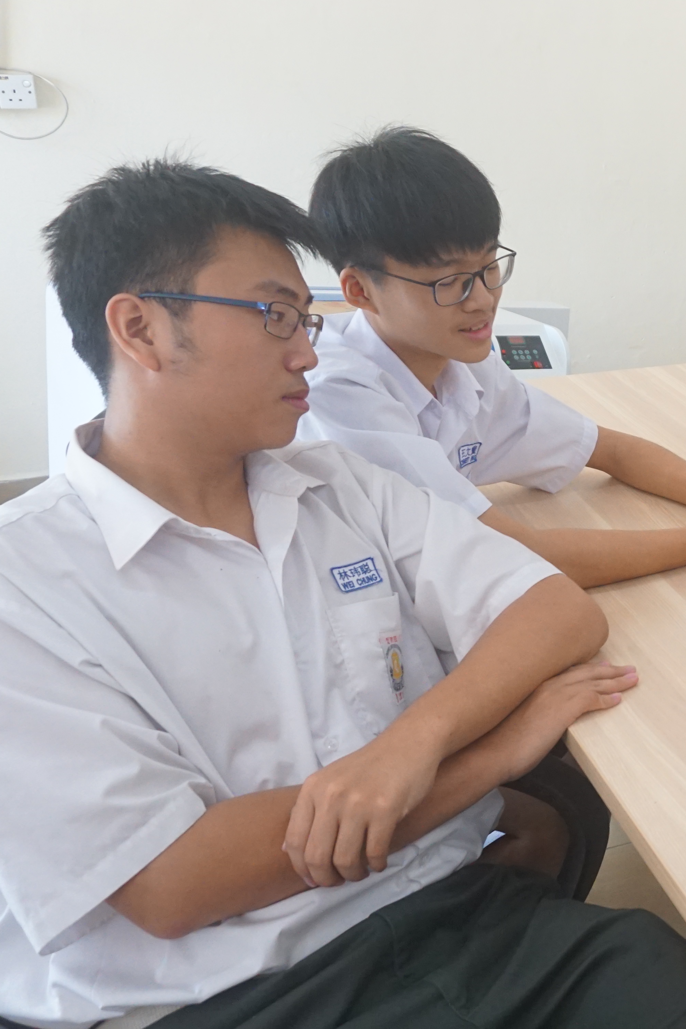
Photos/DSC05798.JPG
