xian-cong/Swalk-Stick/Photos/DSC05800.JPG

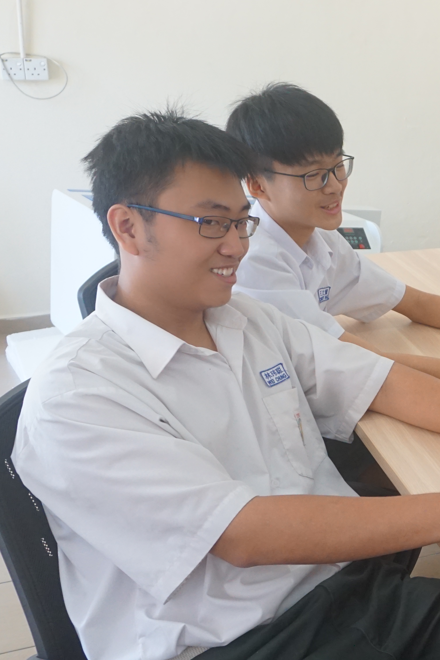
Photos/DSC05800.JPG
