xian-cong/Swalk-Stick/Photos/DSC05802.JPG

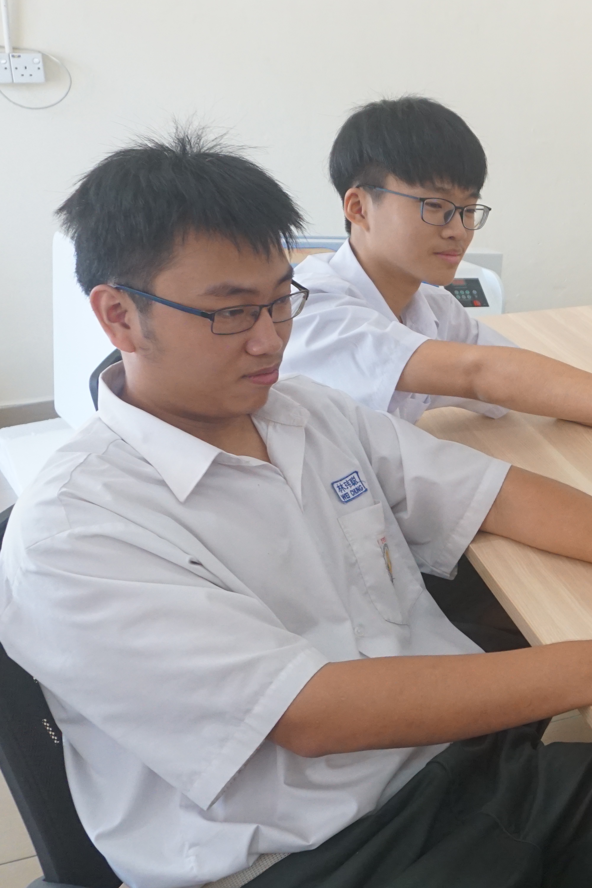
Photos/DSC05802.JPG
