xian-cong/Swalk-Stick/Photos/DSC05804.JPG

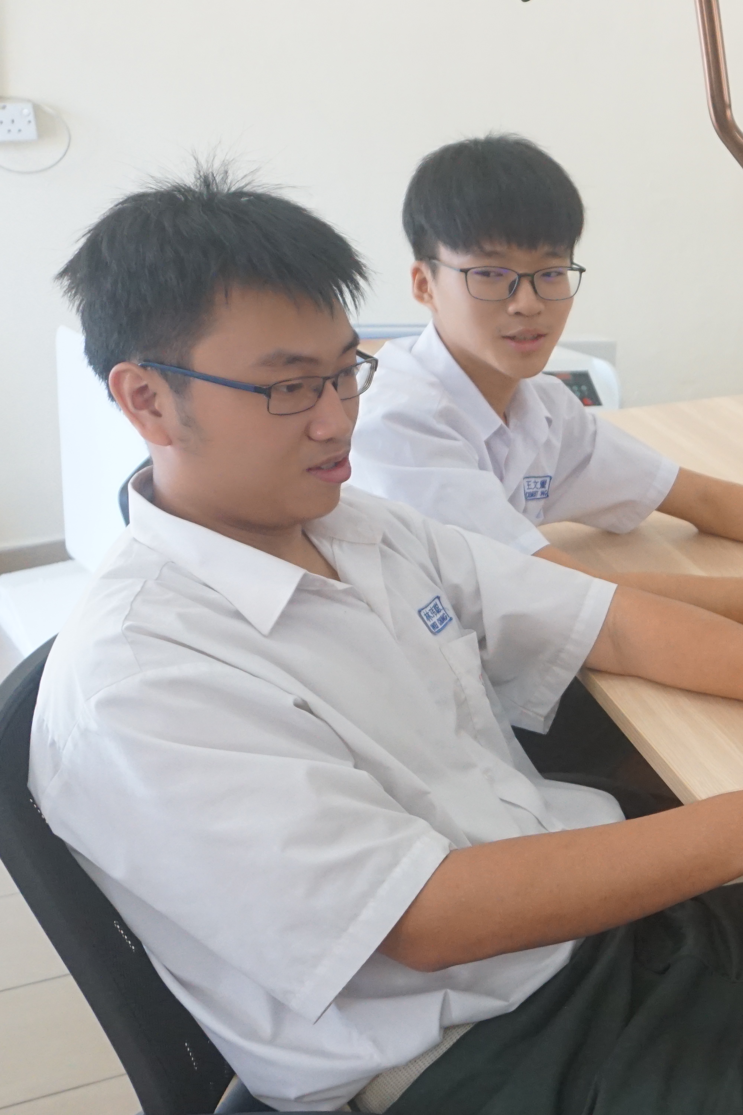
Photos/DSC05804.JPG
