xian-cong/Swalk-Stick/Photos/DSC05809.JPG

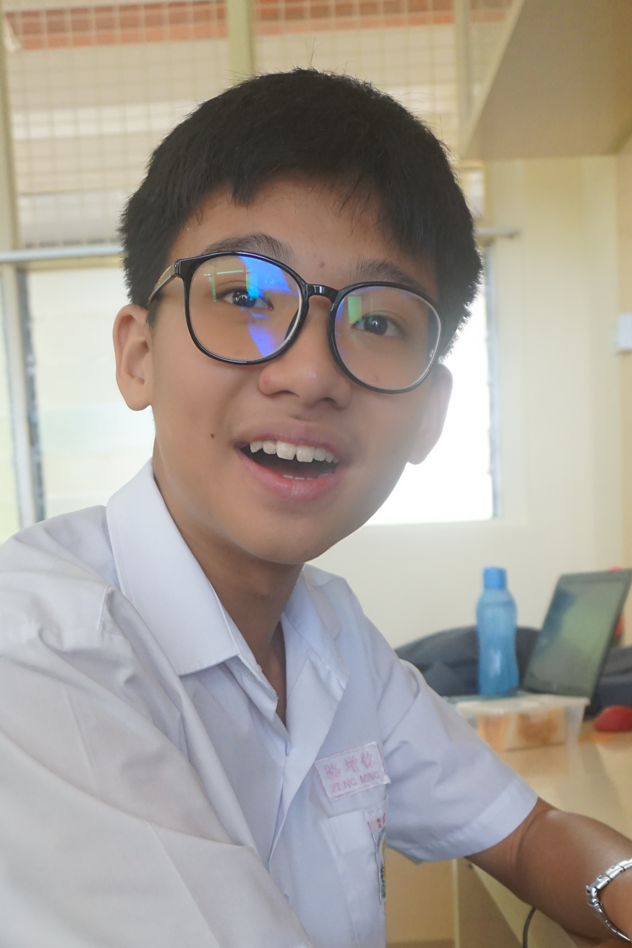
Photos/DSC05809.JPG
