xian-cong/Swalk-Stick/Photos/DSC05811.JPG

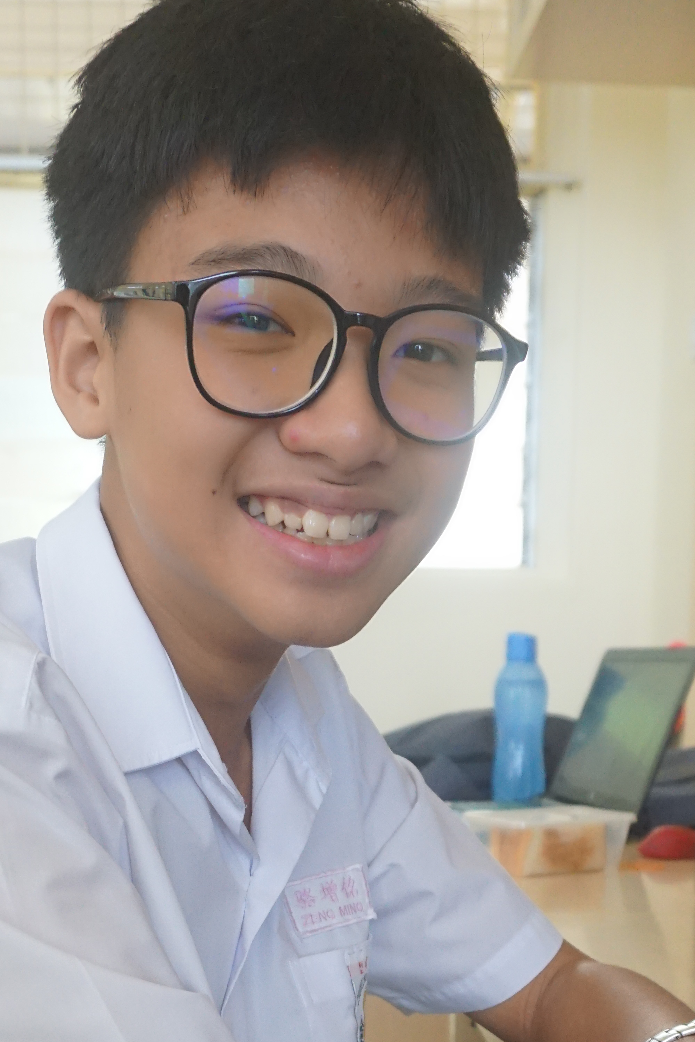
Photos/DSC05811.JPG
